Zille9/ESP32-Basic/IMG/amstrad.JPG

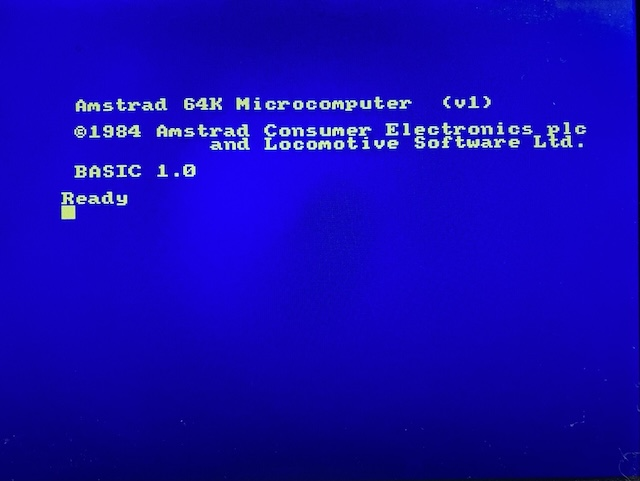
IMG/amstrad.JPG
