Zille9/ESP32-Basic/IMG/App-Starter.JPG

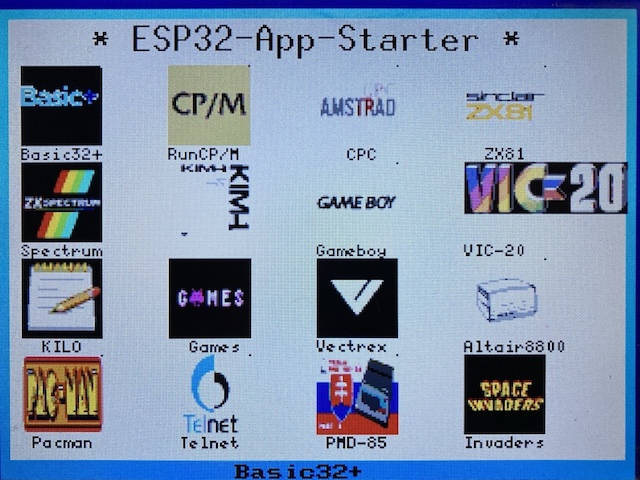
IMG/App-Starter.JPG
