Zille9/ESP32-Basic/IMG/cpc.JPG

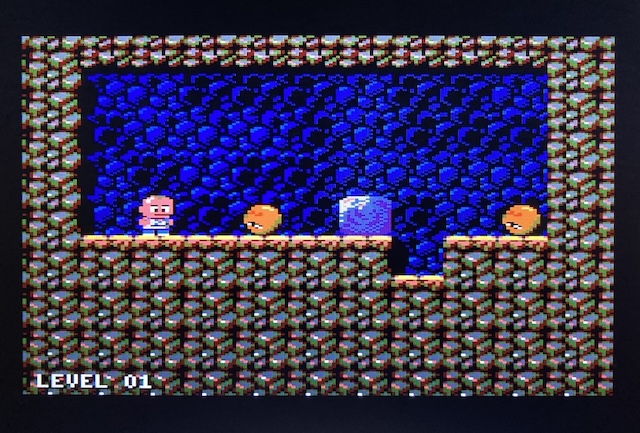
IMG/cpc.JPG
