Zille9/ESP32-Basic/IMG/kilo.JPG

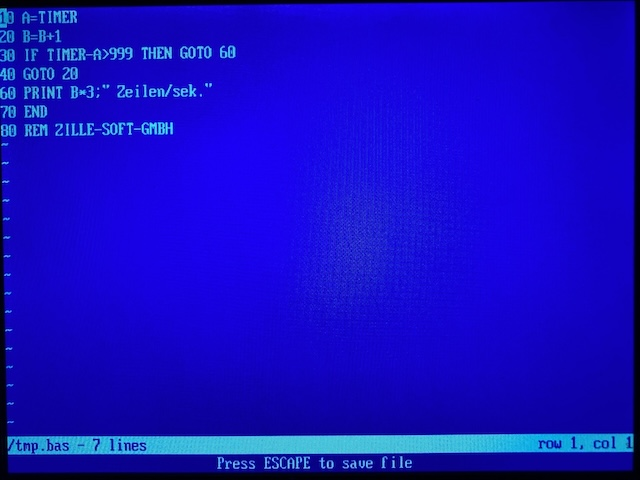
IMG/kilo.JPG
