Zille9/ESP32-Basic/IMG/kim1.JPG

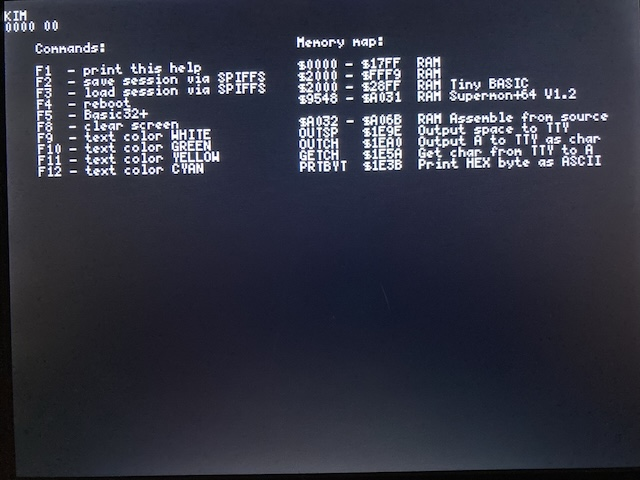
IMG/kim1.JPG
