Zille9/ESP32-Basic/IMG/pacman.JPG

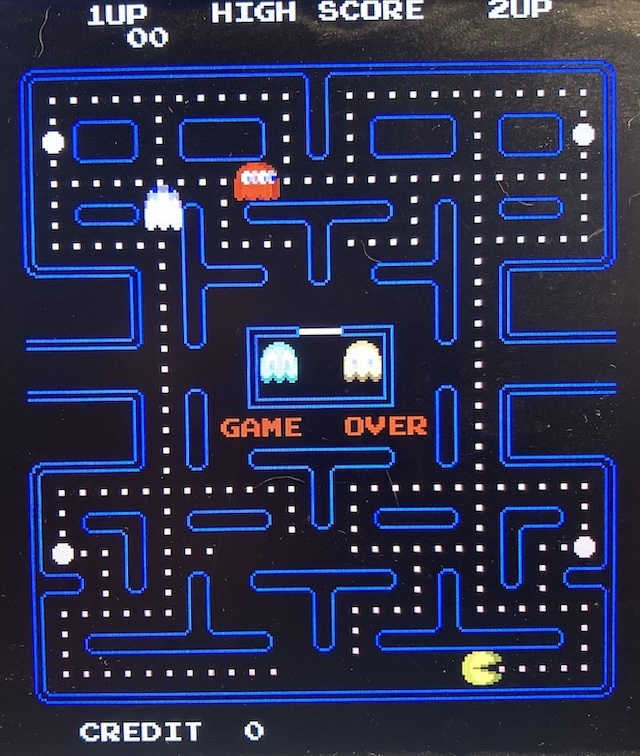
IMG/pacman.JPG
