Zille9/ESP32-Basic/IMG/pmd-85.JPG

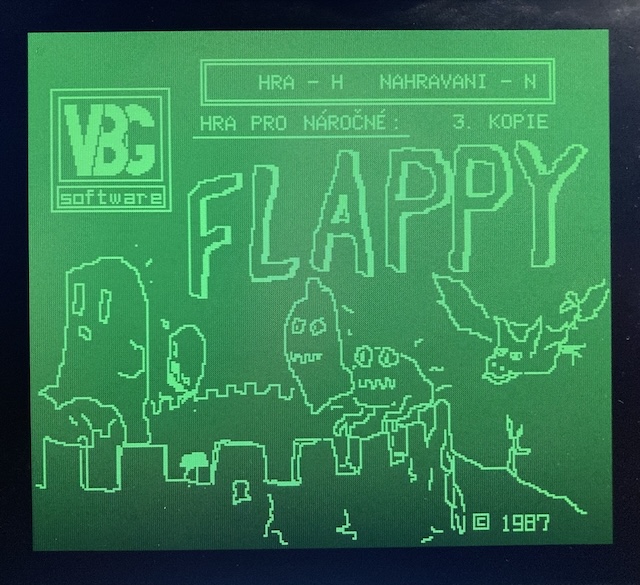
IMG/pmd-85.JPG
