Zille9/ESP32-Basic/IMG/telnet.JPG

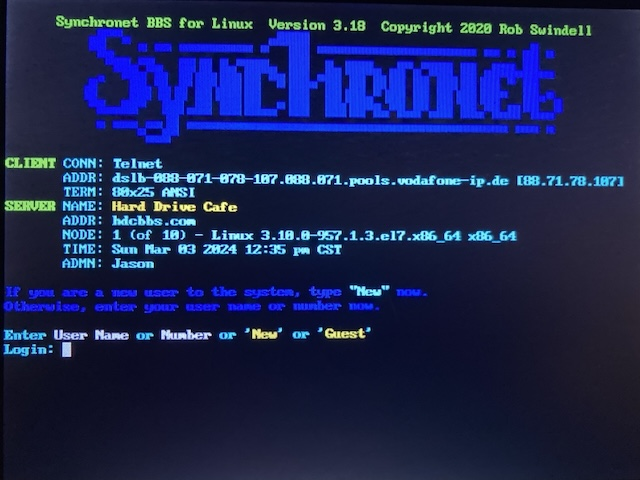
IMG/telnet.JPG
