Zille9/ESP32-Basic/IMG/vectrex.JPG

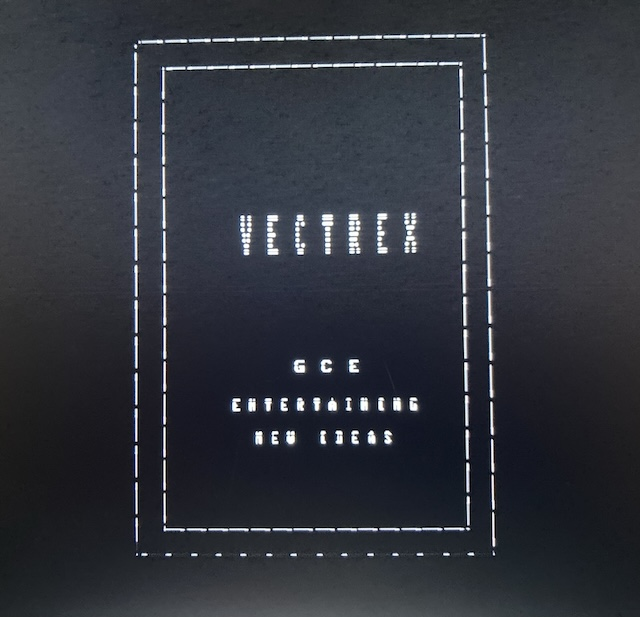
IMG/vectrex.JPG
