Zille9/ESP32-Basic/IMG/vic20.JPG

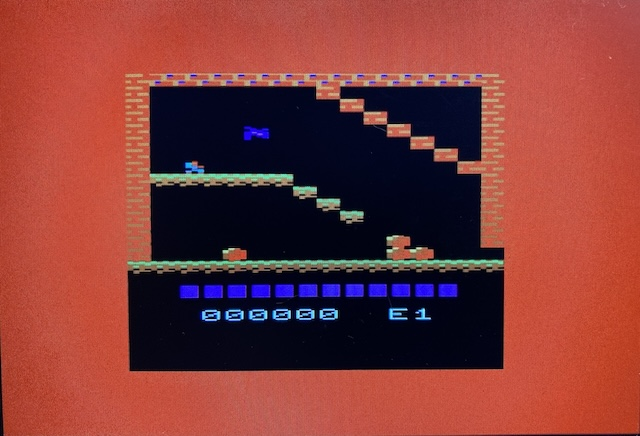
IMG/vic20.JPG
