Zille9/ESP32-Basic/IMG/Webradio.jpg

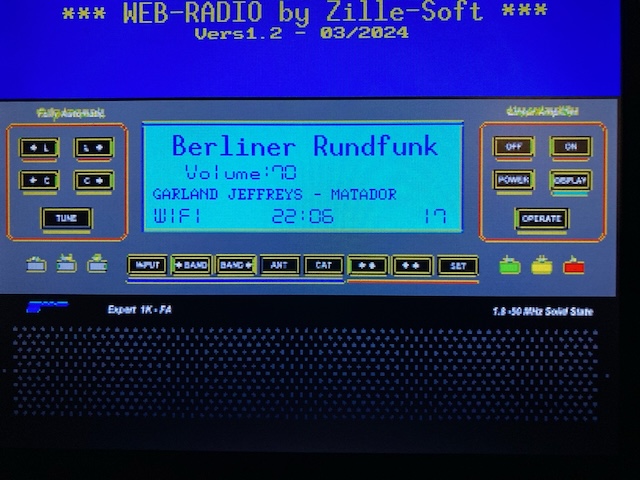
IMG/Webradio.jpg
