Zille9/ESP32-Basic/src/FabGl-Basic/FabGl-Basic.ino

 ///////////////////////////////////////////////////////////////////////////////////////////////////////////////////////////////////////////////////
//             Basic32+ with FabGL VGA library + PS2 PS2Controller                                                                                //
//               for VGA monitor output - May 2019                                                                                                //
//                                                                                                                                                //
//      Ursprungsversion von: Rob Cai <rocaj74@gmail.com>                                                                                         //
//      erweitert/modifiziert von:Reinhard Zielinski <zille09@gmail.com>                                                                          //
//                                                                                                                                                //
//      Connections:                                                                                                                              //
//      PS2Controller Data to ESP32 pin 32;                                                                                                       //
//      PS2Controller IRQ (clock) to ESP32 pin 33;                                                                                                //
//      VGA RGB to ESP32 pin 21,22, 18,19 and 4,5                                                                                                 //
//      VGA Hsync and Vsync to ESP32 pins 23 and 15                                                                                               //
//      SD-Card 14, 16, 17, 13 (SCK, MISO, MOSI, CS)             ESP32-Eigenboard                                                                 //
//      SD-Card 14, 2, 12, 13 (SCK, MISO, MOSI, CS)              TTGO 1.4                                                                         //
//      RAM-Board 14, 16, 17, 0 (SCK, MISO, MOSI, CS)            128,512 o. 8000kB RAM am SD-SPI-BUS                                              //
//      TFT-ILI9341 18, 23, 22, 21, 5 (SCK, MOSI, DC, RESET, CS) TFT-Display ILI9341                                                              //
//                                                                                                                                                //
////////////////////////////////////////////////////////////////////////////////////////////////////////////////////////////////////////////////////
//
// Hinweis: Um die SD-Karte zu verwenden, diese Pinconfiguration verwenden: 14, 16, 17, 13 (SCK, MISO, MOSI, CS)
//          -> Kompatibilität zu fabgl-Programmen (VIC20 Emu, CPM-Emu, ZX-Emu, Tiny-CPC usw.)
//
// Authors: Mike Field <hamster@snap.net.nz>
//	        Scott Lawrence <yorgle@gmail.com>
//          Brian O'Dell <megamemnon@megamemnon.com>
//
// Die Version meiner Vor-Authoren bildet die Grundlage für einen erweiterten Basic-Interpreter
// die Grundversion wurde erweitert durch:  -fliesskomma Arithmetik
//                                          -Grafikfunktionen
//                                          -mathematische Funktionen
//                                          -Stringfunktionen
//                                          -lange Variablennamen
//                                          -viele zusätzliche Befehle (DATA,READ,STRG$,LEFT$,RIGHT$,MID$,POS,TAB,SPC,SIN,COS,TAN,ATN,LOG,SQR,PI usw.)
//                                          -erweiterte logische Operatoren (AND, OR)
//                                          -BIT-Manipulation &,|,%,SL,SR usw.
//                                          -Klammerrechnung
//                                          -IF THEN ELSE Abfragen
//                                          -Speichermonitor
//                                          -Exponential-Ein/Ausgabe
//                                          -Verschiedene Sensoren und Komponenten HC-S04, Dallas DS18S20, DHT, LCD, Neopixel-LED, BMP180
//                                          -Zeileneditor + Texteditor KILO
//                                          -integrierte Kurzhilfe
//
// Author:Reinhard Zielinski <zille09@gmail.com>
// April 2021
//
//
#define BasicVersion "2.06b"
#define BuiltTime "10.05.2024"
// siehe Logbuch.txt zum Entwicklungsverlauf
// v2.06b:10.05.2024          -Fehler in Scroll-Funktion - Anzahl der Parameter war falsch
//                            -16179 Zeilen/sek.
//
// v2.05b:13.04.2024          -Eingabeprompt im Stil des C64 geändert (READY. statt OK>)
//                            -Startbildschirm etwas geschrumpft - Systeminfo's jetzt über F10 abrufbar
//                            -Routine color_out verbessert - keine überstehenden Farbbalken mehr
//                            -16164 Zeilen/sek.
//
// v2.04b:07.04.2024          -Card-KB Treiber etwas angepasst (repeatfunktion) - ZX81 funktioniert (etwas hakelig aber es funktioniert)
//                            -Tastatur wird jetzt auch zuverlässig erkannt
//                            -Ctrl-Tasten-Funktion im Card-KB Treiber eingebunden -> Fn + Buchstabe - Ctrl-C somit wieder funktionstüchtig
//                            -CLEAR löscht jetzt immer die Array-Tabelle (bisher nur, wenn Arrays deklariert waren) - muss vor der ersten Array-Declaration aufgerufen werden (siehe "SOMBRERO.BAS")
//                            -Anzeigeteil der Systemparameter in separate Datei ausgelagert
//                            -Befehl GPX erweitert GPX(x,y,<mode>) mode=0 gibt Pixel gesetzt(1) oder nicht(0) zurück, mode=1 gibt Pixelfarbe zurück
//                            -15972 Zeilen/sek
//
// v2.03b:05.04.2024          -Treiber der Eigenbau-Tastatur ist jetzt zufriedenstellend funktionsfähig, dadurch wurde es nötig die Keyboard-Layout - Umschaltung über den OPT-Befehl
//                            -wieder zugänglich zu machen, das spart die Neucompilierung bei Verwendung unterschiedlicher Tastaturen (Layout steht im EEPROM-Platz 15)
//                            -die Card-KB - Eigenbau - Tastatur erfordert das japanische Layout (Layout 9)
//                            -I2C-Problem mit dem neuen Board, offensichtlich reichen die Pullups des RTC-Moduls für SDA und SCL nicht (bei Netzteilbetrieb), es sind (zumindest für SDA) auf dem Board Pullups notwendig.
//                            -da die Leitungen auf IO1 und IO3 (RX TX) hängen fiel das mit bestehender USB-Verbindung nicht auf (Pegel war hoch genug) - Änderung im Bord-Layout eingepflegt
//                            -und im bestehenden Board zusätzlichen Widerstand eingelötet :-( ärgerlich! -> bei 3,3V muss der Pullup-Widerstand der SDA-Leitung bei ca.2kOhm liegen
//                            -PS2-Treiber der Eigenbau-Tastatur funktioniert nicht bei allen App's - offensichtlich verhält sich eine echte PS2-Tastatur etwas anders als der Eigenbau
//                            -funktionierende Apps: Basic32+, Kilo, VIC20, CPC, ZXESP, Webradio, MP3-Player, Games, ESP-Starter, CPM, Altair, PMD85, Vectrex, Telnet, Invaders - teilweise Tastenanpassungen nötig (Webradio, MP3-Player, Altair, Telnet)
//                            -nicht funktionierende Apps: ESP81, Pacman, Kim1, Gameboy -> keine Reaktion auf Tasteneingaben - Anderer Keyboardtreiber
//                            -SD-Card-Behandlung erweitert - wenn keine oder fehlerhafte Karte detektiert wird
//
// v2.02b:26.03.2024          -neues Board eingetroffen, mit dem es möglich ist SPI-RAM (23LC1024) oder vielleicht sogar PSRAM zu testen, das würde den teuren FRAM ersetzen
//                            -FRAM-Library von Adafruit gekürzt, es wurde die Abfrage der Device-ID deaktiviert. Lt.Datenblatt sollte normaler SPI-RAM und sogar PSRAM ansprechbar sein
//                            -erste Tests bestätigen die Kompatibilität des Treibers für 23LC1024-SPI-Ram Chips - lesen und schreiben funktioniert
//                            -neuer Test mit PSRAM 8MB :-D erfolgreich, somit sind 8MB SPI-Speicher verfügbar allerdings funktioniert alles nur im normalen SPI-Modus
//                            -DSPI oder QSPI sind damit natürlich nicht möglich aber hallo - 8MB, was will man mehr - ist sogar schon etwas zuviel, mal sehen, was mir dazu noch einfällt
//                            -man hat somit 3 unterschiedliche Möglichkeiten der RAM-Unterstützung 128kB-SPI-RAM, 512kB FRAM, 2..4..8MB PSRAM
//                            -FRAM hat den grossen Vorteil, die Daten im ausgeschalteten Zustand nicht zu verlieren und die gleiche Geschwindigkeit und Schreibzyklen (unbegrenzt) wie SPI-Ram zu haben
//                            -ARC-Routine umgebaut, es wird keine cos-Tabelle mehr gebraucht - die Konvertierung Rad in Deg wird berechnet, ausserdem ist die Darstellung genauer
//                            -16500 Zeilen/sek.
//
// v2.01b:19.03.2024          -Grafikbefehl ANGLE erstellt, zeichnet eine Linie von x,y mit dem Winkel w und der länge l -> ANGLE x,y,w,l
//                            -Bildschirmauflösung 320x200 60Hz in fabglconf.h hinzugefügt -> C64 Auflösung, macht die Portierung von Programmen leichter
//                            -Überlegung der Umschaltbarkeit der Auflösungen 320x240 und 320x200 zu integrieren -> funktioniert leider nicht zufriedenstellend
//                            -Umschaltung erfolgt über den OPTION Befehl -> OPT VMODE = mode -> 0 = 320x240, 1 = 320x200(C64 CPC), 2 = 256x192 (ZX Spectrum,TI99), 3=320x256 (KC85), 4=320x192 (Atari 800) und anschliessendem Reboot
//                            -15912 Zeilen/sek - 320x240 , 16500 Zeilen/sek - 320x200, 13539 Zeilen/sek. - 400x300
//
// v2.00b:09.03.2024          -mp3-Player hinzugefügt - ist noch rudimentär aber funktioniert ->RUN"/filename.mp3"
//                            -momentan wird der ID3-Tag als Text ausgeworfen
//                            -ob der Player einen eigenen Befehl (z.Bsp.Play) erhält, ist noch nicht ganz klar (start, stop, pause, nächster- und vorheriger Titel wären nicht schlecht)
//                            -Fehler in der Clear-Routine behoben, es wurden die Variablen im FRam nicht korrekt gelöscht.
//                            -Grafikbefehl ARC erstellt, zeichnet ein Kreis-Teilstück (Tortenstück) ARC x, y, rmin, rmax, grad_start, grad_end, fill
//                            -Grafikbefehl COPY erstellt -> kopiert einen Bildschirmbereich an eine andere Stelle COPY x, y, x_dest, y_dest, width, heigh
//                            -Grafikbefehl SWAP erstellt -> vertauscht die Vorder-und Hintergrundfarbe in einen rechteckigen Bereich SWAP x,y,xx,yy
//                            -16575 Zeilen/sek.
//
//
////////////////////////////////////////////////////////////////////////////////////////////////////////////////////////////////////////////////////
// Konfiguration Grafiktreiber und Akku-Überwachung
#include "cfg.h"   //********************************************* Konfigurations-Datei *************************************************************
#include "fabgl.h" //********************************************* Bibliotheken zur VGA-Signalerzeugung *********************************************
fabgl::Terminal         Terminal;
fabgl::LineEditor       LineEditor(&Terminal);


//---------------------------------------- die verschiedenen Grafiktreiber --------------------------------------------------------------------------
#ifdef AVOUT
fabgl::CVBS16Controller VGAController;    //AV-Variante
#define VIDEOOUT_GPIO GPIO_NUM_26         //Ausgabe auf GPIO25 oder 26 möglich ACHTUNG!:Soundausgabe erfolgt auf GPIO25
static const char * MODES_STD[]   = { "I-PAL-B", "P-PAL-B", "I-NTSC-M", "P-NTSC-M", "I-PAL-B-WIDE", "P-PAL-B-WIDE", "I-NTSC-M-WIDE", "P-NTSC-M-WIDE", "P-NTSC-M-EXT",};

#elif defined VGA64
fabgl::VGAController    VGAController;      //VGA-Variante

#else
fabgl::ILI9341Controller VGAController;     //TFT-Display ILI9341
#endif
//-------------------------------------------------------------------------------------------------------------------------------------------------


//------------------------------------------ Tastatur,GFX-Treiber- und Terminaltreiber -------------------------------------------------------------
fabgl::PS2Controller    PS2Controller;
fabgl::Keyboard Keyboard;
fabgl::Canvas           GFX(&VGAController);
TerminalController      tc(&Terminal);
byte v_mode = 0;                             //Standard-Bildschirmauflösung 320x240
//-------------------------------------------------------------------------------------------------------------------------------------------------

#define erststart_marker 131                //dieser Marker steht im EEprom an Position 100 - wird der ESP32 zum ersten mal mit dem Basic gestartet werden standard-Werte gesetzt
//damit eine benutzbare Version gestartet wird
//---------------------------------------------------- verfügbare Themes ---------------------------------------------------------------------------
const char * Themes[]    PROGMEM = {"C64", "C128", "CPC", "ATARI 800", "ZX-Spectrum", "KC87", "KC85", "VIC-20", "TRS-80", "TI99", "LCD", "User"}; //Theme-Namen
const char * Keylayout[] PROGMEM = {" ", "US", "UK", "GE", "IT", "ES", "FR", "BE", "NO", "JP"};
byte x_char[]      PROGMEM = {8, 5, 6, 8,  10, 8,  8,  8,  8,  8,  8,  8,  8,  6,  8,  4, 6,  7,  7,  8, 8, 8, 6, 9, 8, 8, 6}; //x-werte der Fontsätze zur Berechnung der Terminalbreite
byte y_char[]      PROGMEM = {8, 8, 8, 14, 20, 14, 14, 16, 16, 14, 14, 14, 16, 10, 14, 6, 12, 13, 14, 9, 14, 14, 10, 15, 16, 8, 8}; //y-werte der Fontsätze zur Berechnung der Terminalhöhe

////////////////////////////////////////////////////////////////////////////////////////////////////////////////////////////////////////////////////
//------------------------------------------------------------- Soundgenerator ----------------------------------------------------------------------------
unsigned int noteTable []  PROGMEM = {16350, 17320, 18350, 19450, 20600, 21830, 23120, 24500, 25960, 27500, 29140, 30870}; //Notentabelle für Soundausgabe
//------------------------------------------------------------- Soundgenerator ----------------------------------------------------------------------------

//----------------------------------- Editor -Marker ----------------------------------------------------------------------------------------------
byte Editor_marker = 101;            // EEPROM-Platz 101 beinhaltet den Editor-marker (123) lädt die Datei tmp.bas nach Rückkehr vom Kilo-Editor
//-------------------------------------------------------------------------------------------------------------------------------------------------

// ---------------------------------- SD-Karten-Zugriff--------------------------------------------------------------------------------------------
#include <SD.h>
#include <SPI.h>
//SPI CLASS FOR REDEFINED SPI PINS !
SPIClass spiSD(HSPI);
File fp;
//-------------------------------------------------------------------------------------------------------------------------------------------------

//------------------------------------- OTA-Update-Lib --------------------------------------------------------------------------------------------
#include <Update.h>
//-------------------------------------------------------------------------------------------------------------------------------------------------
/*
//------------------------------------- SPRITES --------------------------------------------------------------------------------------------
#include <collisiondetector.h>
//-------------------------------------------------------------------------------------------------------------------------------------------------
*/

//------------------------------------- ESP32-Time-Lib fuer Datei-zeitstempel ---------------------------------------------------------------------
#include <ESP32Time.h>
ESP32Time e_rtc(0);  // offset in seconds GMT+1
//-------------------------------------------------------------------------------------------------------------------------------------------------

//------------------------------------- Mathematische Funktionen fuer printnum --------------------------------------------------------------------
#include "MathHelpers.h"
//-------------------------------------------------------------------------------------------------------------------------------------------------


// ------------------------------ Dallas Temp-Sensor ----------------------------------------------------------------------------------------------
#include <OneWire.h>
#include <DallasTemperature.h>
bool twire = false;
//-------------------------------------------------------------------------------------------------------------------------------------------------

//--------------------------------- DHT-Sensor ----------------------------------------------------------------------------------------------------
#include <Adafruit_Sensor.h>
#include <DHT.h>
#include <DHT_U.h>
uint32_t delayMS;
//-------------------------------------------------------------------------------------------------------------------------------------------------

//-------------------------------- BMP180-Sensor --------------------------------------------------------------------------------------------------
#include <Adafruit_Sensor.h>
#include <Adafruit_BMP085.h>
// Store an instance of the BMP180 sensor.
Adafruit_BMP085 bmp;
// Store the current sea level pressure at your location in Pascals.
float seaLevelPressure = SENSORS_PRESSURE_SEALEVELHPA;
//-------------------------------------------------------------------------------------------------------------------------------------------------

// -------------------------- EEPROM Routinen für Parameter-Speicherung ---------------------------------------------------------------------------
#include <EEPROM.h>
#define EEPROM_SIZE 512  //512 byte lesen/speichern
//-------------------------------------------------------------------------------------------------------------------------------------------------

//---------------------------- EEPROM o.FRAM-Chip I2C-Adressen ------------------------------------------------------------------------------------

short int EEprom_ADDR = 0x50; //-> Adresse 0x50 ist der EEPROM auf dem Board
//short int EEprom_ADDR = 0x57; //-> Adresse 0x57 ist der EEPROM auf dem RTC3231 Board
//-------------------------------------------------------------------------------------------------------------------------------------------------


// ---------------------------- W2812-seriell LED-Treiber -----------------------------------------------------------------------------------------
#include <Adafruit_NeoPixel.h>
unsigned int LED_COUNT      = 255;
unsigned int LED_PIN        = 2;
unsigned int LED_BRIGHTNESS = 50;
unsigned int LED_TYP        = 2;
Adafruit_NeoPixel strip(LED_COUNT, LED_PIN, NEO_GRB + NEO_KHZ800);                //WS2812
//-------------------------------------------------------------------------------------------------------------------------------------------------

//------------------------------ MCP23017 IO-Expander ---------------------------------------------------------------------------------------------
#include <Adafruit_MCP23X17.h>   //Adafruit MCP23xx Treiber
Adafruit_MCP23X17 mcp;
short int MCP23017_ADDR = 0x20 ; //Adresse 32 (0x20) für eingebauten MCP23017
bool mcp_start_marker = false;
//-------------------------------------------------------------------------------------------------------------------------------------------------

//------------------------------ I2C Library ------------------------------------------------------------------------------------------------------
#include <Wire.h>           // for I2C 
#include "RTClib.h"         //to show time
TwoWire myI2C = TwoWire(0); //eigenen I2C-Bus erstellen
RTC_DS3231 rtc;
//diese Konstellation funktioniert mit ESP-Eigenboard und RTC-Modul oder 27 und 26 für die Freigabe des Seriellports
byte IIC_SET = 55;      // -steht 55 im EEprom-Platz 13, dann sind die Werte im EEprom gültig
// dies ist die Standard-Konfiguration
byte SDA_RTC = 3;
byte SCL_RTC = 1;
//-------------------------------------------------------------------------------------------------------------------------------------------------

//-------------------------------------- LCD-Treiber ----------------------------------------------------------------------------------------------
#include "HD44780_LCD_PCF8574.h"
#define DISPLAY_DELAY_INIT 50 // mS
int LCD_SPALTEN, LCD_ZEILEN, LCD_ADRESSE, LCD_NACHKOMMA;
bool LCD_start_marker = false;
bool LCD_Backlight = true;
//-------------------------------------------------------------------------------------------------------------------------------------------------

//######################################### Anfang Konfiguration SPI-RAM ##########################################################################
//------------------------------------------- SPI-RAM-Lib -----------------------------------------------------------------------------------------
#include "Adafruit_FRAM_SPI.h"        // Library unterstützt 23LC1024, Adafruit SPI-FRAM und PSRAM

byte FRAM_CS  = 0;                    //SPI-RAM CS-Pin
Adafruit_FRAM_SPI spi_fram = Adafruit_FRAM_SPI(kSD_CLK, kSD_MISO, kSD_MOSI, FRAM_CS);

//---------------------------------------- spezielle SPI-Ram-Adressen -----------------------------------------------------------------------------
word FRAM_OFFSET      = 0x8000;     //Offset für Poke-Anweisungen, um zu verhindern, das in den Array-Bereich gepoked wird
word FRAM_PIC_OFFSET  = 0x12C04;    //Platz pro Bildschirm im Speicher 320x240=76800 + 4Byte für die Dimension = 76804
long load_adress      = 0x8000;     //ab hier kann ein Basicprogramm abgelegt werden (Eingabe: LOAD oder SAVE ohne Parameter)

//---------------------------------------- Array-Parameter ----------------------------------------------------------------------------------------
//Der Arraybereich befindet sich 0x0..0x7fff
word Var_Neu_Platz =  0;            //Adresse nächstes Array-Feld Start bei 0x77e00
static word VAR_TBL = 0x7e00;       //Variablen-Array-Tabelle im SPI-RAM
static word STR_TBL = 0x7f00;       //String-Array-Tabelle im SPI-RAM
//-------------------------------------------------------------------------------------------------------------------------------------------------
//######################################### Ende Konfiguration SPI-RAM ############################################################################



//------------------------------- Konfiguration serielle Schnittstelle ----------------------------------------------------------------------------
uint8_t prx, ptx;             //RX- und TX-Pin
uint32_t pbd;                 //Baudrate
bool ser_marker = false;      //seriell-Marker, wenn gesetzt erfolgt jede Printausgabe auch auf die serielle Schnittstelle
bool list_send = false;
bool serout_marker = false;
#define SERIAL_SIZE_RX 1024
//-------------------------------------------------------------------------------------------------------------------------------------------------

//------------------------------------------------ Startparameterauswahl --------------------------------------------------------------------------
byte Keyboard_lang = KLayout; //Tastatur-Layout (cfg.h) - Standardeinstellung=German
byte THEME_SET = 77;    //-steht 77 im EEPROM Platz 17, dann setze das gespeicherte Theme
byte PATH_SET = 88;     //-steht 88 im EEPROM Platz 19, dann setze Arbeits-Pfad
//-------------------------------------------------------------------------------------------------------------------------------------------------

//------------------------------------- Akku-Überwachung ------------------------------------------------------------------------------------------
#ifdef Akkualarm_enabled            // Akku-Überwachung für batteriebetriebene Geräte
hw_timer_t *Akku_timer = NULL;      //Interrupt-Routine Akku-Überwachung
#endif
#define Batt_Pin 39                 //Pin wird in jedem Fall definiert
//-------------------------------------------------------------------------------------------------------------------------------------------------

//------------------------------- BMP-Info-Parameter für PIC-Befehl -------------------------------------------------------------------------------
uint32_t bmp_width, bmp_height;
//-------------------------------------------------------------------------------------------------------------------------------------------------

#define bool int
#define true 1
#define false 0

//für Texte/Zeichenketten im Flash
#ifndef PROGMEM
#define PROGMEM
#endif
#ifndef pgm_read_byte
#define pgm_read_byte( A ) *(A)
#endif

#define STR_LEN 40
#define STR_SIZE 26*STR_LEN             //Stringspeicher = Stringlänge 26*40 Zeichen (A..Z * 40 Zeichen)

//------------------------------ hier wird der Funktionsstring gespeichert ------------------------------------------------------------------------
#define FN_SIZE STR_LEN                 //Funktionsspeicher für benutzerdefinierte Funktionen mit bis zu vier Operatoren-> FN A(A,B,C,D)

bool inhibitOutput = false;
static bool autorun = false;            //Programm nach dem Laden automatisch starten
static bool triggerRun = false;

short int Vordergrund = 43;             //Standard-Vordergrundfarbe (wenn noch nichts im EEprom steht)
short int Hintergrund = 18;             //Standard-Hintergrundfarbe (wenn noch nichts im EEprom steht)
short int fontsatz = 0;                 //Nummer des ausgewählten Fontsatzes
short int user_vcolor = Vordergrund;    //User-Vordergrundfarbe
short int user_bcolor = Hintergrund;    //User-Hintergrundfarbe
short int user_font = fontsatz;         //User-Fontsatz

short int Prezision = 6;                //Standardfestlegung der Nachkommastellen
static bool chr = false;                //marker für CHR$ für Print
static bool string_marker = false;      //marker für Strings (Print)
static bool func_string_marker = false; //marker für String$-Funktion (Print)
static bool tab_marker = false;         //marker für TAB (Print)
static bool semicolon = false;          //marker für semikolon (Print)
static byte fstring = 0;                //Übergabewert für STRING$(n,"string")
short int Theme_state = 0;              //aktuelle Theme Nummer (im EEPROM gespeichert)
static bool Theme_marker = false;       //Theme-Marker, falls Farben geändert
short int Mode_state = 0;               //aktuelle Auflösung (im EEProm gespeichert)

static bool break_marker = false;      //********** Test für CardKB *****************

uint8_t curGain = 100;                 //current loudness Audiolautstärke
int Key_l = 0;                         //Tasten für MP3-Player
int Key_r = 0;
int Key_u = 0;
int Key_d = 0;

//------------------------------ Grid-Parameter ---------------------------------------------------------------------------------------------------
int Grid[15];  //0=x, 1=y, 2=xx, 3=yy, 4=zell_x, 5=zell_y, 6=pix_x, 7=pix_y, 8=frame-col, 9=grid_col
int Grid_point_x, Grid_point_y;

//------------------------------ Window-Parameter -------------------------------------------------------------------------------------------------

int Frame_nr;                 //5 Fenster können erstellt werden
int Frame_x[6];
int Frame_y[6];
int Frame_xx[6];
int Frame_yy[6];
int Frame_curx[6];            //X-Cursor Initialwert
int Frame_curtmpx[6];         //X-Cursor temporärer Wert
int Frame_curtmpy[6];         //Y-Cursor temporärer Wert
int Frame_cury[6];            //Y-Cursor Initialwert
int Frame_col[6];             //Rahmenfarbe
int Cursor_x, Cursor_y;       //temporäre Cursorpositionen
int Frame_vcol[6];            //Vordergrundfarbe
int Frame_hcol[6];            //Hintergrundfarbe
bool Frame_title[6];          //Titeltext
char Frame_ttext[6][STR_LEN]; //Fenster-Titel-String

//-------------------------------------------------------------------------------------------------------------------------------------------------

short int onoff = 1;          //Cursor status

//-------------------------------------------------------------------------------------------------------------------------------------------------

// these will select, at runtime, where IO happens through for load/save
enum {
  kStreamTerminal = 0,
  kStreamFile,
  kStreamSerial,
  kStreamFram
};
static char inStream = kStreamTerminal;
static char outStream = kStreamTerminal;

static char program[kRamSize];            //Basic-Programmspeicher
static char Stringtable[STR_SIZE];        //Stringvariablen mit 1 Buchstaben -> 26*40 = 1040 Bytes
//-------------------------------------------------------------------------------------------------------------------------------------------------

//------------------------------------- DEFN - FN -------------------------------------------------------------------------------------------------
static char Fntable[26][FN_SIZE];         // bytes 40 String = 40*26 ->1040 bytes ->Funktionsstring-Array
int Fnvar = 0;                            //Operatorenzähler
int Fnoperator[27 * 5];                   //DEFN A(a,b,c,d,e,f,g,h)-> Name 0-26,0-26=Operator1,0-26=operator2,0-26=Operator3,0-26=Operator4 + 1 Anzahl
bool fn_marker = false;

//------------------------------------ Editor -----------------------------------------------------------------------------------------------------
char const * Edit_line = nullptr;        //Editor-Zeile
long editpos;                            //Position innerhalb des Programs
//------------------------------------ Interpreter ------------------------------------------------------------------------------------------------
char tempstring[STR_LEN];                //String Zwischenspeicher

//------------------------------------ Dateifunktionen FREAD,FWRITE -------------------------------------------------------------------------------
char filestring[STR_LEN];                //Namensstring für Dateioperationen Fread,Fwrite
static bool Datei_open = false;          //FREAD, FWRITE Open-marker
long File_pos = 0;                       //Dateipositions-merker der geöffneten Datei
long File_size = 0;                      //Dateigrösse der geöffneten Datei

static char *txtpos, *list_line, *tmptxtpos, *dataline;
static char expression_error;
static char *tempsp;
static char sd_pfad[STR_LEN];            //SD-Card Datei-Pfad

char path1[STR_LEN], path2[STR_LEN];     //Variablen für Dateioperationen
unsigned int Datum[4];                   //Datums-Array
unsigned int Zeit[4];                    //Zeit-Array

//----------------------------------------- DATA Variablen ----------------------------------------------------------------------------------------
unsigned int datapointer = 0;       //data-Zeiger innerhalb des Datanfeldes
unsigned int restorepointer = 0;    //begin des Datanfeldes
unsigned int num_of_datalines = 0;  //Anzahl DATA-Zeilen
unsigned int current_dataline = 0;  //aktuelle DATA-Zeile
unsigned int data_numbers[300];     //Array zur speicherung von 300 DATA Zeilennummern

//////////////////////////////////////////////////////////////////////////////////////////////////////////////////////////////////////////////////
// ASCII Characters
#define CR	'\r'
#define NL	'\n'
#define LF  0x0a
#define TAB	'\t'
#define BELL	'\b'
#define SPACE   ' '
#define SQUOTE  '\''
#define DQUOTE  '\"'
#define CTRLC	0x03
#define CTRLH	0x08
#define CTRLS	0x13

bool Graph_char = false;                               //Grafiksymbole "AUS"
bool tron_marker = false;                              //TRON "AUS"

typedef short unsigned LINENUM;

/***************************Basic-Befehle ********************************/
// Keyword table and constants - the last character has 0x80 added to it
const static char keywords[] PROGMEM = {
  'L', 'I', 'S', 'T' + 0x80,
  'L', 'O', 'A', 'D' + 0x80,
  'N', 'E', 'W' + 0x80,
  'R', 'U', 'N' + 0x80,
  'S', 'A', 'V', 'E' + 0x80,
  'N', 'E', 'X', 'T' + 0x80,
  'R', 'E', 'N' + 0x80,
  'I', 'F' + 0x80,
  'G', 'O', 'T', 'O' + 0x80,
  'G', 'O', 'S', 'U', 'B' + 0x80,
  'R', 'E', 'T', 'U', 'R', 'N' + 0x80,
  'R', 'E', 'M' + 0x80,
  'F', 'O', 'R' + 0x80,
  'I', 'N', 'P', 'U', 'T' + 0x80,
  'P', 'R', 'I', 'N', 'T' + 0x80,
  'P', 'O', 'K', 'E' + 0x80,
  'D', 'I', 'R' + 0x80,
  'C', 'L', 'S' + 0x80,
  'P', 'O', 'S' + 0x80,
  'C', 'O', 'L' + 0x80,
  'P', 'S', 'E', 'T' + 0x80,
  'C', 'I', 'R', 'C' + 0x80,
  'L', 'I', 'N', 'E' + 0x80,
  'R', 'E', 'C', 'T' + 0x80,
  'F', 'O', 'N', 'T' + 0x80,
  'P', 'A', 'U', 'S', 'E' + 0x80,
  'E', 'N', 'D' + 0x80,
  'C', 'L', 'E', 'A', 'R' + 0x80,
  'T', 'H', 'E', 'N' + 0x80,
  'E', 'L', 'S', 'E' + 0x80,
  'C', 'U', 'R' + 0x80,
  'P', 'R', 'Z' + 0x80,
  'D', 'M', 'P' + 0x80,
  'S', 'T', 'Y', 'L', 'E' + 0x80,
  'S', 'C', 'R', 'O', 'L', 'L' + 0x80,
  'T', 'H', 'E', 'M', 'E' + 0x80,
  'D', 'A', 'T', 'A' + 0x80,
  'R', 'E', 'A', 'D' + 0x80,
  'R', 'E', 'S', 'T', 'O', 'R', 'E' + 0x80,
  'D', 'E', 'L' + 0x80,
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
};

// by moving the command list to an enum, we can easily remove sections
// above and below simultaneously to selectively obliterate functionality.
enum {
  KW_LIST = 0,
  KW_LOAD,
  KW_NEW,
  KW_RUN,
  KW_SAVE,
  KW_NEXT,
  KW_REN,
  KW_IF,
  KW_GOTO,
  KW_GOSUB,
  KW_RETURN,    //10
  KW_REM,
  KW_FOR,
  KW_INPUT,
  KW_PRINT,
  KW_POKE,
  KW_DIR,
  KW_CLS,
  KW_POS,
  KW_COLOR,
  KW_PSET,      //20
  KW_CIRCLE,
  KW_LINE,
  KW_RECT,
  KW_FONT,
  KW_DELAY,
  KW_END,
  KW_CLEAR,
  KW_THEN,
  KW_ELSE,
  KW_CURSOR,    //30
  KW_PREZISION,
  KW_DUMP,
  KW_STYLE,
  KW_SCROLL,
  KW_THEME,
  KW_DATA,
  KW_READ,
  KW_RESTORE,
  KW_DEL,
  KW_AND,       //40
  KW_OR,
  KW_SRTC,
  KW_IIC,
  KW_DWRITE,
  KW_PWM,
  KW_DAC,
  KW_DRAW,
  KW_SPRITE,
  KW_PULSE,
  KW_SOUND,    //50
  KW_PEN,
  KW_ON,
  KW_LCD,
  KW_MCPPORT,
  KW_MCPPIN,
  KW_CHDIR,
  KW_MKDIR,
  KW_RMDIR,
  KW_DEFFUNC,
  KW_LED,     //60
  KW_EDIT,
  KW_DOKE,
  KW_BEEP,
  KW_DIM,
  KW_OPTION,
  KW_FPOKE,
  KW_MOUNT,
  KW_COM,
  KW_PIC,
  KW_OPEN,    //70
  KW_CLOSE,
  KW_FILE,
  KW_TYPE,
  KW_GRID,
  KW_TEXT,
  KW_PRINTING,
  KW_WINDOW,
  KW_HELP,
  KW_FRAME,
  KW_ARC,     //80
  KW_SWAP,
  KW_COPY,
  KW_ANGLE,
  //KW_BAR,
  KW_DEFAULT  //85/* hier ist das Ende */
};

int KW_WORDS = KW_DEFAULT;

// Variablen zur Zwischenspeicherung von logischen Operationen (AND OR)

int logic_counter;
int logic_ergebnis[10];

//-> bis zu 5 AND oder OR Vergleiche können in einer Zeile vorkommen

struct stack_for_frame {
  char frame_type;    //1byte
  int for_var;        //2byte
  float to_var;       //4byte
  float step;         //4byte
  char *current_line; //1byte
  char *txtpos;       //1byte
};

struct stack_gosub_frame {
  char frame_type;
  char *current_line;
  char *txtpos;
};

#define User_Ram (kRamSize-STACK_SIZE-(26 * 27 * VAR_SIZE))

//**************************** Basic-Funktionen *********************************
const static char func_tab[] PROGMEM = {
  'P', 'E', 'E', 'K' + 0x80,
  'A', 'B', 'S' + 0x80,
  'R', 'N', 'D' + 0x80,
  'S', 'I', 'N' + 0x80,
  'C', 'O', 'S' + 0x80,
  'T', 'A', 'N' + 0x80,
  'L', 'O', 'G' + 0x80,
  'S', 'G', 'N' + 0x80,
  'S', 'Q', 'R' + 0x80,
  'I', 'N', 'T' + 0x80,
  'M', 'I', 'N' + 0x80,
  'M', 'A', 'X' + 0x80,
  'E', 'X', 'P' + 0x80,
  'G', 'E', 'T' + 0x80,
  'C', 'H', 'R', '$' + 0x80,
  'I', 'N', 'K', 'E', 'Y' + 0x80,
  'F', 'O', 'N', 'T' + 0x80,
  'A', 'S', 'C' + 0x80,
  'T', 'I', 'M', 'E', 'R' + 0x80,
  'A', 'T', 'N' + 0x80,
  'L', 'E', 'N' + 0x80,
  'I', 'N', 'S', 'T', 'R' + 0x80,
  'C', 'O', 'M', 'P', '$' + 0x80,
  'B', 'I', 'N' + 0x80,
  'H', 'E', 'X' + 0x80,
  'L', 'E', 'F', 'T', '$' + 0x80,
  'R', 'I', 'G', 'H', 'T', '$' + 0x80,
  'M', 'I', 'D', '$' + 0x80,
  'T', 'A', 'B' + 0x80,
  'S', 'P', 'C' + 0x80,
  'S', 'T', 'R', '$' + 0x80,
  'D', 'A', 'T', 'E' + 0x80,
  'T', 'I', 'M', 'E' + 0x80,
  'I', 'I', 'C' + 0x80,
  'A', 'K', 'K', 'U' + 0x80,
  'A', 'I', 'N' + 0x80,
  'D', 'I', 'N' + 0x80,
  'U', 'C', '$' + 0x80,
  'L', 'C', '$' + 0x80,
  'V', 'A', 'L' + 0x80,
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
};

enum {
  FUNC_PEEK = 0,
  FUNC_ABS,
  FUNC_RND,
  FUNC_SIN,
  FUNC_COS,
  FUNC_TAN,
  FUNC_LOG,
  FUNC_SGN,
  FUNC_SQR,
  FUNC_INT,
  FUNC_MIN,     //10
  FUNC_MAX,
  FUNC_EXP,
  FUNC_GET,
  FUNC_CHR,
  FUNC_INKEY,
  FUNC_FONT,
  FUNC_ASC,
  FUNC_TIMER,
  FUNC_ATAN,
  FUNC_LEN,       //20
  FUNC_INSTR,
  FUNC_COMPARE,
  FUNC_BIN,
  FUNC_HEX,
  FUNC_LEFT,
  FUNC_RIGHT,
  FUNC_MID,
  FUNC_TAB,
  FUNC_SPC,
  FUNC_STR,       //30
  FUNC_GDATE,
  FUNC_GTIME,
  FUNC_IIC,
  FUNC_BATT,
  FUNC_AREAD,
  FUNC_DREAD,
  FUNC_UCASE,
  FUNC_LCASE,
  FUNC_VAL,
  FUNC_MEM,      //40
  FUNC_NOT,
  FUNC_TEMP,
  FUNC_DHT,
  FUNC_GETCOL,
  FUNC_BMPREAD,  //ungetestet BMP180 Drucksensor
  FUNC_FN,
  FUNC_PORT,
  FUNC_PIN,
  FUNC_PI,
  FUNC_LN,       //50
  FUNC_DEEK,
  FUNC_FPEEK,
  FUNC_GPIX,
  FUNC_PIC,
  FUNC_MAP,
  FUNC_CONSTRAIN,
  FUNC_STRING,
  FUNC_FILE,
  FUNC_GRID,
  FUNC_UNKNOWN   //60
};

int FUNC_WORDS = FUNC_UNKNOWN;

//------------------------------- OPTION-Tabelle - alle Optionen, die dauerhaft gespeichert werden sollen -----------------------------------------
const static char options[] PROGMEM = {
  'V', 'M', 'O', 'D', 'E' + 0x80,           //VGA-Modus 0=320x240, 1=320x200
  'F', 'R', 'A', 'M' + 0x80,                //CS-Pin FRAM
  'E', 'E', 'P', 'R', 'O', 'M' + 0x80,      //Adresse des I2C-EEproms
  'F', 'O', 'N', 'T' + 0x80,                //Font dauerhaft speichern
  'C', 'O', 'L' , 'O', 'R' + 0x80,          //Vordergrund- und Hintergrundfarbe dauerhaft speichern
  'K', 'E', 'Y' + 0x80,                     //Keyboardlayout 1=US,2=UK,3=GE,4=IT,5=ES,6=FR,7=BE,8=NO,9=JP
  'T', 'H', 'E', 'M', 'E' + 0x80,           //THEME
  'P', 'A', 'T', 'H' + 0x80,                //Arbeitsverzeichnis

  0
};

enum {
  OPT_VMODE = 0,
  OPT_FRAM,
  OPT_EEP,
  OPT_FONT,
  OPT_COLOR,
  OPT_KEYBOARD,
  OPT_THEME,
  OPT_PATH,
  OPT_UNKNOWN  //8
};
//-------------------------------------------------------------------------------------------------------------------------------------------------


const static char to_tab[] PROGMEM = {
  'T', 'O' + 0x80,
  0
};

const static char step_tab[] PROGMEM = {
  'S', 'T', 'E', 'P' + 0x80,
  0
};

const static char relop_tab[] PROGMEM = {
  '>', '=' + 0x80,  //größer gleich
  '<', '>' + 0x80,  //ungleich
  '>', '>' + 0x80,  //SHIFT RIGHT
  '>' + 0x80,       //größer
  '=' + 0x80,       //gleich
  '<', '=' + 0x80,  //kleiner gleich
  '<', '<' + 0x80,  //SHIFT LEFT
  '|', '|' + 0x80,  //XOR
  '<' + 0x80,       //kleiner
  '%' + 0x80,       //MODULO
  '&' + 0x80,       //AND
  '|' + 0x80,       //OR
  '^' + 0x80,       //POW
  0
};

#define RELOP_GE		0
#define RELOP_NE		1
#define RELOP_SHR   2
#define RELOP_GT		3
#define RELOP_EQ		4
#define RELOP_LE		5
#define RELOP_SHL   6
#define RELOP_XOR   7
#define RELOP_LT		8
#define RELOP_MOD   9
#define RELOP_AND   10
#define RELOP_OR    11
#define RELOP_POW   12
#define RELOP_UNKNOWN	13

#define STACK_SIZE (sizeof(struct stack_for_frame)*26)   // 26 verschachtelte For-Next-Schleifen erlaubt (32bytes pro frame) 
#define VAR_SIZE sizeof(float)                           // Variablengrösse für float 4Bytes
static char *stack_limit;
static char *program_start;
static char *program_end;
static char *stack; // Software stack for things that should go on the CPU stack
static char *variables_begin;
static char *current_line;
static char *data_line;
static char *sp;
#define STACK_GOSUB_FLAG 'G'
#define STACK_FOR_FLAG 'F'
static char table_index;
static char keyword_index;
static LINENUM linenum;

//---------------------------------- Fehlermeldungen des Interpreters -----------------------------------------------------------------------------

static const char syntaxmsg[]        PROGMEM = "Syntax Error! ";                //1
static const char mathmsg[]          PROGMEM = "Math Error!";                   //2
static const char gosubmsg[]         PROGMEM = "Gosub Error!";                  //3
static const char fornextmsg[]       PROGMEM = "For-Next Error!";               //4
static const char memorymsg[]        PROGMEM = " bytes free";
static const char missing_then[]     PROGMEM = "Missing THEN Error!";           //5
static const char breakmsg[]         PROGMEM = "Break! in Line:";
static const char breaks[]           PROGMEM = "Break!";
static const char datamsg[]          PROGMEM = "Out of DATA Error!";            //6
static const char invalidmsg[]       PROGMEM = "Invalid comparison!";           //7
static const char sderrormsg[]       PROGMEM = "SD card error.";                //8
static const char sdfilemsg[]        PROGMEM = "SD file error.";                //9
static const char dirextmsg[]        PROGMEM = "(dir)";
static const char slashmsg[]         PROGMEM = "/";
static const char spacemsg[]         PROGMEM = " ";
static const char notexistmsg[]      PROGMEM = "File not exist!";               //10
static const char portmsg[]          PROGMEM = "Wrong Port-Number!";            //11
static const char valmsg[]           PROGMEM = "Invalid Value!";                //12
static const char dirmsg[]           PROGMEM = "Dir not empty!";                //13
static const char illegalmsg[]       PROGMEM = "Illegal quantity Error!";       //14
static const char zeroerror[]        PROGMEM = "Div/0-Error!";                  //15
static const char outofmemory[]      PROGMEM = "Out of Memory Error!";          //16
static const char mountmsg[]         PROGMEM = "SD-Card mounted";               //17
static const char notmount[]         PROGMEM = "SD-Card can't mount";           //18
static const char dimmsg[]           PROGMEM = "Array-Dimension Error!";        //19
static const char commsg[]           PROGMEM = "No COM-Port defined!";          //20
static const char comsetmsg[]        PROGMEM = "Wrong COM-Port Definition!";    //21
static const char bmpfilemsg[]       PROGMEM = "No BMP-File!";                  //22
static const char no_prg_msg[]       PROGMEM = "No Program in Memory !";        //23
static const char no_command_msg[]   PROGMEM = "Keyword not found !";           //24
static const char not_openmsg[]      PROGMEM = "File not open Error !";         //25
static const char dirnotfound[]      PROGMEM = "DIR not found !";               //26
static const char extension_error[]  PROGMEM = "invalid File-Extension !";      //27
//----------------------------------- Interpreter-Variablen ---------------------------------------------------------------------------------------
char *pstart;
char *newEnd;
char linelen;
bool then_marker = false;
bool else_marker = false;
float val;
int Zahlenformat = 0;
int logica = 0;                          //logikzähler für IF abfragen
unsigned int ongosub = 0;                //ON-Gosub Goto marker
//----------------------------------- Interpreter-Variablen ---------------------------------------------------------------------------------------
//#################################################################################################################################################
//############################################# Ende Deklarationsungsbereich ######################################################################
//#################################################################################################################################################

//--------------------------------------------- Ausgabe Fehlermeldungen ---------------------------------------------------------------------------
static char syntaxerror(const char *msg)
{
  printmsg(msg, 1);
  if (current_line != NULL)
  {
    char tmp = *txtpos;           //Position merken
    if (*txtpos != NL) *txtpos = '^';
    list_line = current_line;
    printline();
    *txtpos = tmp;                //gemerkte Position zurückschreiben
  }
  Beep(0, 0);                     //Error-BEEP
  current_line = 0;
  line_terminator();
}

float NoteToFreq(int mnote)
{
  int octave;
  octave = mnote / 12;
  mnote -= octave * 12;
  return noteTable[mnote] >> (8 - octave);
}

void Beep(int n, int len)
{
  if (n == 0) n = 60;
  if (len == 0) len = 100;
  if (n > 80) n = 80;
  if (n < 20) n = 20;
  n = NoteToFreq(n);
  //SND(waveform,frequency,duration,volume)

  Terminal.print("\e_S0;" + String(n, DEC) + ";" + String(len, DEC) + ";126$");
  delay(len);
}

//--------------------------------------------- Unterprogramm - Zeichen überspringen --------------------------------------------------------------
//--------------------------------------------- nächstes Zeichen zurückgeben ----------------------------------------------------------------------

static char skip_spaces(void) {
  if (*txtpos)
  {
    txtpos++;
    return spaces();
  }
}


//--------------------------------------------- Unterprogramm - Leerzeichen überspringen ----------------------------------------------------------
//--------------------------------------------- erstes gültiges Zeichen zurückgeben ---------------------------------------------------------------

static char spaces(void) {                      //Leerzeichen oder Tab überspringen
  char c;
  while (1) {
    c = *txtpos;
    if (c == SPACE || c == TAB) txtpos++;
    else break;
  }
  return (c);
}

//--------------------------------------------- Unterprogramm - Befehls-und Funktionstabellen lesen -----------------------------------------------

static void scantable(const char *table)
{
  int i = 0;
  table_index = 0;

  while (1)
  {
    // Keine Tabelleneinträge mehr?
    if (pgm_read_byte( table ) == 0)
      return;

    // Passt das Zeichen??
    if (txtpos[i] == pgm_read_byte( table ))
    {
      i++;
      table++;
    }
    else
    {
      //Wort komplett, dann zurück
      if (txtpos[i] + 0x80 == pgm_read_byte( table ))
      {
        txtpos += i + 1;
        spaces();
        return;
      }

      while ((pgm_read_byte( table ) & 0x80) == 0)
        table++;

      // Fortfahren mit dem ersten Zeichen des nächsten Wortes, Positionsindex zurücksetzen
      table++;
      table_index++;
      spaces();
      i = 0;
    }
  }
}


//--------------------------------------------- Unterprogramm - Zahlenausgabe ---------------------------------------------------------------------

void printnum(float num, int modes)   //Ausgabe als float
{ char c[32];
  float tmp;
  int stellen;
  String stz;
  int len;
  unsigned long hexnum;
  String cbuf;

  switch (modes)
  {
    case 0:                                       //normale Zahlenausgabe
      if (num > 9999999 || num < -9999999) {
        printmsg(sci(num, Prezision), 0);         //Ausgabe in Exponential-Schreibweise
      }

      else {
        tmp = num - int(num);                     //Nachkommastelle vorhanden oder 0 ?
        if (tmp == 0) {                           //keine Nachkommastelle
          itoa(num, c, 10);
          printmsg(c, 0);                         //dann Integerausgabe

        }
        else {                                    //Nullen in der Nachkommastelle sollen abgeschnitten werden
          dtostrf(num, 1, Prezision, c);          //Nullen abschneiden
          stz = c;
          len = stz.length();
          stellen = Prezision;
          for (int i = len - 1; i > 0; i--) {
            if ((c[i] > '0') || (c[i] == '.')) break; //keine Null oder komma?
            if (c[i] == '0') stellen -= 1;
          }
          dtostrf(num, 1, stellen, c);                //formatierte Ausgabe ohne Nullen
          printmsg(c, 0);
        }
      }
      break;

    case 1:                                           //Ausgabe als Binärzahl
      hexnum = num;
      outchar('%');
      itoa(num, c, 2);
      printmsg(c, 0);
      Zahlenformat = 0;
      break;

    case 2:                                           //Ausgabe als Hexadezimalzahl
      outchar('#');
    case 3:                                           //Ausgabe als Hexadezimalzahl für Memory_dump ohne #
      hexnum = num;
      itoa(num, c, 16);
      printmsg(c, 0);
      Zahlenformat = 0;
      break;

    default:
      break;
  }//switch(modes)
}

//#######################################################################################################################################
//--------------------------------------------- DUMP - Befehl ---------------------------------------------------------------------------
//#######################################################################################################################################

static int Memory_Dump() {                       //DMP Speichertyp 0..2 <,Adresse>
  int ex = 0, c, was, tpm;
  int ln = (VGAController.getScreenHeight() / y_char[fontsatz]) - 3; //Anzahl Zeilen abhängig vom Fontsatz
  //if (Frame_nr) win_set_cursor(0);               //sind Fenster gesetzt?, dann Hauptfenster setzen
  int x_weite = VGAController.getScreenWidth() / x_char[fontsatz];

#ifdef ILI9341                                  //bei TFT x und y vertauscht
x_weite = (VGAController.getScreenHeight() / x_char[fontsatz]) ;
ln = VGAController.getScreenWidth() / y_char[fontsatz] - 3;    //Anzahl Zeilen abhängig vom Fontsatz
#endif

  byte rdbyte[8];

  word of = FRAM_OFFSET;
  long n;
  long adr = 0;
  was = abs(int(get_value()));                  //nur ganze Zahlen
  if (*txtpos == ',')
  {
    txtpos++;
    adr = abs(get_value());                      //nur ganze Zahlen
  }

  if (*txtpos == 'V') {
    of = 0;                                       //wird V angegeben, kann man den Variablenbereich ansehen
    txtpos++;
  }


  if (was > 2) {
    syntaxerror(syntaxmsg);
    return 1;
  }
  //spi_fram.begin(3);
  while (!ex) {
    for (int i = 1; i < ln; i++)
    {
      if (adr < 0x1000)outchar('0');
      if (adr < 0x100)outchar('0');
      if (adr < 0x10)outchar('0');
      n = adr;
      printnum(adr, 3);                                 //Hexausgabe
      outchar(' ');

      for (int f = 0; f < 8; f++) {                     //8 Speicherplätze lesen und anzeigen
        switch (was) {
          case 1:  //FRAM
            if (spi_fram.read8(of + n) < 16) outchar('0');
            printnum(spi_fram.read8(of + n++), 3);
            if (x_weite > 39) outchar(' ');                       //wenn genug Platz, dann Leerzeichen zwischen den Werten
            break;
          case 2:  //EEPROM
            if (readEEPROM(EEprom_ADDR, n ) < 16) outchar('0');
            printnum(readEEPROM(EEprom_ADDR, n++ ), 3);
            if (x_weite > 39) outchar(' ');
            break;
          default:  //interner RAM
            if (program[int(n)] < 16) outchar('0');
            printnum(program[int(n++)], 3);
            if (x_weite > 39) outchar(' ');
            break;
        }
      }
      if (x_weite < 40) outchar(' ');                             //wenn nicht genug Platz, dann nur ein Leerzeichen nach 8Bytes


      for (int i = 0; i < 8; i++) {
        switch (was) {
          case 1:  //FRAM
            c = spi_fram.read8(of + adr++);//readEEPROM(FRam_ADDR, adr++);
            break;
          case 2:  //EEPROM
            c = readEEPROM(EEprom_ADDR, adr++);
            break;
          default:  //interner RAM
            c = program[int(adr++)];
            break;
        }

        if (c > 31 && c < 127)
          outchar(c);
        else
          outchar('.');
      }
      line_terminator();
    }
    if (wait_key(true) == 3) ex = 1;    //Ctrl-C oder ESC Abbruch

  }//while (ex)
  return 0;
}

//--------------------------------------------- Unterprogramm teste auf gültige Zeilennummer ------------------------------------------------------

static unsigned short testnum(void)               // Überprüfung auf Zeilennummer -> Zeilennummern > 65535 erzeugen einen Überlauf (es fängt wieder bei 1 an)
{
  unsigned int num = 0;
  spaces();

  while (*txtpos >= '0' && *txtpos <= '9' )
  {
    num = num * 10 + *txtpos - '0';
    txtpos++;
  }
  return	num;
}

//--------------------------------------------- Unterprogramm - Fehler/Nachrichtausgabe -----------------------------------------------------------

void printmsg(const char *msg, int nl)
{
  //fbcolor(Vordergrund, Hintergrund);                                //Themen-Farben setzen ist nötig, sonst fällt der Interpreter in die Terminalfarben zurück
  //if (Frame_nr) fbcolor(Frame_vcol[Frame_nr], Frame_hcol[Frame_nr]); //Wenn Fenster, dann Fensterfarben
  while ( pgm_read_byte( msg ) != 0 )
  {
    outchar( pgm_read_byte( msg++ ) );
  }

  if (nl == 1) line_terminator();
}

//--------------------------------------------- Unterprogramm - Tastenabfrage (list-Ausgaben) -----------------------------------------------------

static unsigned short wait_key(bool modes) {
  char c;
  if (modes)
  {
    line_terminator();//Terminal.println();
    printmsg("SPACE<Continue>/CTR+C or ESC<Exit>", 1);
  }
  while (1) {
    if (Terminal.available())
    {
      c = Terminal.read();
      break;
    }
    if (break_marker == true)
    {
      c = 3;
      break_marker == false;
      break;
    }
  }
  return c;
}

//--------------------------------------------- Unterprogramm - Zeile eingeben --------------------------------------------------------------------

static void getln(int m)//char prompt)
{ int chpos = -1;
  if (m) 
  {
    outchar('R');
    outchar('E');
    outchar('A');
    outchar('D');
    outchar('Y');
    outchar('.');
    line_terminator();
  }
  //outchar(prompt);

  txtpos = program_end + sizeof(LINENUM);

  while (1)
  {

    char c = inchar();
    if (c == 27 && Frame_nr) continue;


    switch (c)
    {
      case NL:

      case CR:
        line_terminator();
        // Terminate all strings with a NL
        txtpos[0] = NL;
        return;

      case 0x7F:

        if (txtpos == program_end)
          break;


        if (Frame_nr) {                   //im Fenster kein Backspace, um das Fenster nicht zu beschädigen
          Cursor_x = tc.getCursorCol();
          Cursor_y = tc.getCursorRow();
          tc.setCursorPos(tc.getCursorCol() - 1, Cursor_y);
          tc.setChar(' ');
          tc.setCursorPos(tc.getCursorCol() - 1, Cursor_y);
        }
        else if (chpos > -1) {
          chpos--;
          txtpos--;
          Terminal.write("\b\e[K");      //nicht im Fenster, dann Backspace
        }

        break;
      case 0x03:       // ctrl+c
        line_terminator();
        printmsg(breaks, 1);
        current_line = 0;
        sp = program + sizeof(program);
        txtpos[0] = NL;
        return;
        break;

      default:
        // Wir müssen mindestens ein Leerzeichen lassen, damit wir die Zeile in die richtige Reihenfolge bringen können
        if (txtpos == variables_begin - 2)
          outchar(CTRLH);
        else
        {
          txtpos[0] = c;
          txtpos++;
          chpos++;
          outchar(c);

        }
    }
  }

}


//--------------------------------------------- Unterprogramm - Programmzeile finden ---------------------------------------------------------------
static char *findline(void)
{
  char *line = program_start;
  while (1)
  {
    if (line == program_end)
      return line;

    if (((LINENUM *)line)[0] >= linenum)
      return line;

    // Add the line length onto the current address, to get to the next line;
    line += line[sizeof(LINENUM)];
  }
}


//--------------------------------------------- Unterprogramm - Data-zeile finden -----------------------------------------------------------------

static char *find_data_line(void)
{
  char *line = program_start;
  while (1)
  {
    if (line == program_end)
      return 0;

    dataline = line + sizeof(LINENUM) + sizeof(char);         //Programmzeile übergeben

    if (dataline[0] == 'D' && dataline[1] == 'A' && dataline[2] == 'T' && dataline[3] == 'A')
    {
      data_numbers[num_of_datalines++] = *((LINENUM *)line);
    }
    // Add the line length onto the current address, to get to the next line;
    line += line[sizeof(LINENUM)];
  }
  num_of_datalines -= 1;
  return 0;
}

//--------------------------------------------- Unterprogramm - Grossbuchstabenumwandlung ---------------------------------------------------------

static void toUppercaseBuffer(void)
{
  char *c = program_end + sizeof(LINENUM);
  char quote = 0;

  while (*c != NL)
  {
    // Are we in a quoted string?
    if (*c == quote)
      quote = 0;
    else if (*c == '"' || *c == '\'')
      quote = *c;
    else if (quote == 0 && *c >= 'a' && *c <= 'z')
      *c = *c + 'A' - 'a';
    c++;
  }
}

//--------------------------------------------- Unterprogramm - Zeile ausgeben (Bildschirm oder Datei) --------------------------------------------

int printline(void)
{ int digits = 0;
  int num;
  LINENUM line_num;

  line_num = *((LINENUM *)(list_line));
  list_line += sizeof(LINENUM) + sizeof(char);

  num = line_num;

  printnum(num, 0);

  outchar(' ');
  while (*list_line != NL)
  {
    outchar(*list_line);
    list_line++;
  }

  list_line++;
  line_terminator();
  return line_num;
}

//--------------------------------------------- Unterprogramm - RTC auslesen ----------------------------------------------------------------------

void getdatetime()
{
  DateTime now = rtc.now();           //RTC Funktion
  Zeit[0] = now.hour();
  Zeit[1] = now.minute();
  Zeit[2] = now.second();
  Datum[0] = now.day();
  Datum[1] = now.month();
  Datum[2] = now.year();
  Datum[3] = now.dayOfTheWeek();
  e_rtc.setTime(Zeit[2], Zeit[1], Zeit[0], Datum[0], Datum[1], Datum[2], 0);
}

//--------------------------------------------- Unterprogramm - Hexadezimalzahl in Dezimalzahl konvertieren ---------------------------------------

static int hexDigit(char c)
{
  if (c >= '0' && c <= '9')
    return c - '0';
  if (c >= 'A' && c <= 'F')
    return c - 'A' + 10;
  if (c >= 'a' && c <= 'f')
    return c - 'a' + 10;
  return -1;
}


/*************************************************************************************************************************************************/
//--------------------------------------------- Start - Werteausgabe ------------------------------------------------------------------------------
//--------------------------------------------- Zahlen,Variablen oder Strings auslesen ------------------------------------------------------------
//--------------------------------------------- logische Abhängigkeiten auswerten -----------------------------------------------------------------
//--------------------------------------------- mathematische Funtionen ausführen -----------------------------------------------------------------
/*************************************************************************************************************************************************/
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
void loop()
{

  //--------------------------------------------- hier geht's los -----------------------------------------------------------------------------------
  Basic_Interpreter();
}


//********************************************* Main - Programm ***********************************************************************************


//#################################################################################################################################################
//############################################# Start Basic_Interpreter ###########################################################################
//#################################################################################################################################################

void Basic_Interpreter()
{
  char pa, pb;
  initSD();                                              //SD-Karte initialisieren
  cmd_new();                                             //alles löschen
  print_info();                                          //Start-Bildschirm anzeigen
  check_editor();                                        // befindet sich im EEPROM-Platz 50 die 123, dann die datei tmp.bas automatisch laden
  int a, e;

  //################################################# Hauptprogrammschleife ######################################################
  while (1)
  {

    expression_error = 0;                               //alle Errors zurücksetzen

    if ( triggerRun ) {                                 // AUTO-START-FUNKTION
      triggerRun = false;
      clear_var();                                      //Variablen und Array-Tabelle löschen, Data-Zeiger zurücksetzen
      find_data_line();                                 //Data-Zeilen finden
      current_line = program_start;
      sp = program + sizeof(program);
      goto execline;
    }

    else {
      getln(1);
      //-------------------------------- Start Zeile einfügen ---------------------------------------------
      move_line();                                                  //Zeile in Großbuchstaben umwandeln und ans Ende des Speicher verschieben
      linenum = testnum();                                          // Zeilennummer vorhanden?
      spaces();
      if (linenum == 0) {
        if (direct() == 0) continue;                                //keine Zeilennummer
        else goto interpreteAtTxtpos;                               //Zeile ausführen
      }
      if (insert_line()) {                                          //Zeile in die richtige Position im Speicher einfügen oder löschen, wenn kein Text vorhanden
        continue;
      }
    }
    //------------------------------------------ Ende Zeile einfügen -------------------------------------------------
    continue;


run_next_statement:

    if (run_next() == 1) goto execnextline;

interpreteAtTxtpos:

    if (breakcheck() || break_marker)                                //Programmabbruch mit Ctrl-C oder ESC
    {
      break_marker = false;
      line_terminator();

      if (current_line != NULL)
      {
        printmsg(breakmsg, 0);
        linenum = *((LINENUM *)(current_line));
        printnum(linenum, 0);
        //if(ser_marker) Serial1.print(linenum);
      }

      line_terminator();
      warmstart();
      Terminal.enableCursor(true);                                 //Cursor einschalten
      continue;

    }

    scantable(keywords);                                            //Befehlstabelle scannen
    keyword_index = table_index;


    //####################################################################################################
    //############################### Abarbeitung Befehlstabelle #########################################
    //####################################################################################################

    switch (keyword_index)
    {
      case KW_LIST:                                       // LIST
        list_out();
        continue;
        break;


      case KW_LOAD:                                       // LOAD filename
        if (*txtpos == NL) {
          load_ram();
          continue;
        }

        if (load_file()) {
          continue;
        }
        string_marker = false;
        continue;
        break;

      case KW_NEW:                                        // NEW
        cmd_new();
        continue;
        break;

      case KW_RUN:                                        // RUN
        if (*txtpos == '"') {                             //RUN"/Filename" lädt und startet das Programm
          if (load_file()) {
            continue;
          }
          string_marker = false;
          autorun = true;
        }
        if (*txtpos == '*') {
          load_ram();
        }
        clear_var();
        find_data_line();                                 //Data-Zeilen finden
        current_line = program_start;                     //beginn mit erster Zeile
        sp = program + sizeof(program);
        goto execline;
        break;

      case KW_SAVE:                                       // SAVE filename (/filename.bas)
        if (*txtpos == NL) {
          save_ram();
          continue;
        }
        save_file();
        string_marker = false;
        continue;
        break;

      case KW_NEXT:                                       // NEXT
        goto next;
        break;

      case KW_REN:                                        // RENAME
        expression_error = 0;
        get_value();
        strcpy(filestring, tempstring);       //Tempstring nach filestring kopieren
        if (Test_char(',')) continue;
        get_value();
        renameFile(SD, filestring, tempstring);
        continue;
        break;

      case KW_IF:                                         // IF
        float val;
        logic_counter = 0;
        logica = 0;
        else_marker = false;
        then_marker = true;                               //THEN marker muss noch abgefragt werden (missing_then)
        memset (logic_ergebnis, 0, sizeof (logic_ergebnis));//Logik-Puffer leeren
        expression_error = 0;
        val = get_value();
        logic_ergebnis[logic_counter++] = int(val);       //Ergebnis in Puffer speichern und logicmarker hochzählen
        if (val != 0) {
          val = 0;                                        //für den Fall, das kein AND,OR vorkommt
          break;
        }
        else
        {
          else_marker = true;
          val = 1;                                        //Für den Fall, das es kein AND OR gibt (einfaches IF)
          goto run_next_statement;                        //die ELSE Bedingung muss in der nächsten Zeile stehen
        }
        break;

      case KW_ON:                                         //ON (GOTO/GOSUB)
        ongosub = 0;
        ongosub = get_value();
        if (ongosub == 0) goto execnextline;              //ist der Wert der Variable=0 dann wird mit der nächsten Zeile weitergemacht
        break;

      case KW_GOTO ... KW_GOSUB:                          // GOTO/GOSUB
        expression_error = 0;
        linenum = get_value();
        if (ongosub > 0)
        {
          e = 1;
          while (*txtpos == ',' && e < ongosub)           //so oft wiederholen, wie Zeilennummern existieren
          {
            txtpos++;
            e++;
            linenum = get_value();
          }

          if (a < 0 || a > 65535)
          {
            //syntaxerror(syntaxmsg);
            continue;
          }
        }
        if (keyword_index == KW_GOSUB)
        {
          gosub();
        }

        current_line = findline();
        goto execline;
        break;

      case KW_RETURN:                                     // RETURN
        goto gosub_return;
        break;

      case KW_REM:                                        // REM
        goto execnextline;                                // Ignoriere die komplette Zeile
        break;

      case KW_FOR:
        goto forloop;
        break;

      case KW_INPUT:
        if (input()) continue;
        break;

      case KW_PRINTING:                                   // ?
      case KW_PRINT:                                      // Print
        if (command_Print()) continue;
        break;

      case KW_DOKE:
      case KW_POKE:                                       // POKE adresse,wert
      case KW_FPOKE:
        if (poke(keyword_index)) continue;
        break;

      case KW_DIR:                                        // SD-Card Directory DIR
        cmd_Dir();
        continue;
        break;

      case KW_CHDIR:                                      // SD-Card Change-Directory CD
        cmd_chdir();
        break;

      case KW_MKDIR:                                      // SD-Card Make-Dir MD
        if (cmd_mkdir(1));
        continue;
        break;

      case KW_RMDIR:                                      // SD-Card Remove-Dir RD
        if (cmd_mkdir(0));
        continue;
        break;

      case KW_CLS:                                        // CLS
        if (Frame_nr) {
          win_cls(Frame_nr);
        }
        else {
          tc.setCursorPos(1, 1);
          //cmd_cls();
          GFX.clear();
        }
        break;

      case KW_POS:                                        // POS x,y
        if (set_pos())
          continue;
        break;

      case KW_COLOR:                                      // COLOR v,b
        if (color())
          continue;
        break;

      case KW_PSET:                                       // PSET x,y
        if (pset())
          continue;
        break;

      case KW_CIRCLE:                                     // CIRCLE x,y,w,h,fill
        if (line_rec_circ(1, 4))                          //1=Circle, 0..4 Parameter
          continue;
        break;

      case KW_LINE:                                       // LINE x,y,xx,yy
        if (line_rec_circ(0, 3))                          // 0=Lines, 0..3 Parameter
          continue;
        break;

      case KW_RECT:                                       // RECT x,y,w,h,fill
        if (line_rec_circ(2, 4))                          // 2=Rect, 0..4 Parameter
          continue;
        break;

      case KW_FRAME:                                      // FRAME x,y,w,h,r
        if (line_rec_circ(3, 4))                          // 3=Round, 0..4 Parameter
          continue;
        break;

      case KW_ARC:                                        // ARC x,y,rmin,rmax,gstart,gend,fill
        if (line_rec_circ(4, 6))
          continue;
        break;
      /*
      case KW_BAR:
        if(line_rec_circ(10,5))                           //BAR x, y, orient, w, h, wert
          continue;
        break;
        */
      case KW_SWAP:
        if (line_rec_circ(5, 3))                          //SWAP x,y,xx,yy ->vertauscht vorder und Hintergrundfarbe eines rechtecks
          continue;
        break;

      case KW_COPY:
        if (line_rec_circ(6, 5))                          //Copy x,y,x_dest,y_dest, w, h ->Kopiert ein Rechteck von x,y nach x_dest,y_dest mit der Größe w,h
          continue;
        break;

      case KW_ANGLE:
        if (line_rec_circ(9, 3))
          continue;
        break;

      case KW_FONT:                                       // FONT f
        expression_error = 0;
        val = int(get_value());
        set_font(val);
        break;

      case KW_DELAY:                                       //PAUSE
        expression_error = 0;
        val = get_value();
        delay( val );
        break;

      case KW_END:
        current_line = program_end;
        goto execline;
        break;

      case KW_CLEAR:
        Var_Neu_Platz = 1;                                //auch Array-Ram auf jeden Fall löschen
        clear_var();
        break;

      case KW_THEN:                                      // THEN
        then_marker = false;
        if ( val == 0 ) {                                //Überprüfung, ob alle If Bedingungen war sind
          break;
        }
        else
        {
          else_marker = true;
          goto execnextline;                             //Bedingung nicht erfüllt -> nächste Zeile
        }

      case KW_ELSE:                                       // ELSE
        if (else_marker == true) {
          else_marker = false;
          break;
        }
        goto execnextline;                                //Bedingung nicht erfüllt -> nächste Zeile

      case KW_CURSOR:
        if (cursor_onoff())
          continue;
        break;

      case KW_PREZISION:                                  // PREZ 6 ->Nachkommastellen
        if (set_prezision())
          continue;
        break;

      case KW_DUMP:                                       // DUMP adresse
        if (Memory_Dump())
          continue;
        break;

      case KW_STYLE:
        if (set_style())
          continue;
        break;

      case KW_SCROLL:
        if (line_rec_circ(8, 1))
          continue;
        break;

      case KW_THEME:
        int a;
        a = int(get_value());
        set_theme(a);
        print_info();
        break;

      case KW_DATA:                                       // DATA - wird ignoriert
        goto execnextline;
        break;

      case KW_READ:
        while (1) {
          if (data_get())
          {
            syntaxerror(datamsg);
            continue;
          }
          if (*txtpos == ',')
            txtpos++;
          else break;
        }
        break;

      case KW_RESTORE:                                                //setzen des Datazeigers
        if (*txtpos == NL || *txtpos == ':')                          //wird kein Wert gelesen, datapointer zurücksetzen
        {
          string_marker = false;
          datapointer = 0;
          current_dataline = 0;
        }
        else
        {
          expression_error = 0;                                       //es wird eine Zeilennummer angegeben
          linenum = get_value();
          for (int i = 0; i <= (num_of_datalines - 1); i++)           //scannen, ob Zeilennummer existiert, wenn ja, übernehmen
          {
            if (data_numbers[i] == linenum)
            {
              datapointer = 0;                                       //datapointer zurücksetzen
              current_dataline = i;                                  //Zeiger auf die exitierende Zeile setzen
              break;
            }
          }
        }
        break;

      case KW_DEL:                                        // DEL
        if (cmd_delFiles())
        {
          syntaxerror(notexistmsg);
        }
        continue;
        break;

      case KW_AND:
        expression_error = 0;
        val = get_value();
        logic_ergebnis[logic_counter++] = int(val);       //alle Ergebnisse einlesen und auswerten
        for (int i = 0; i < logic_counter + 1; i++)
        {
          logica += logic_ergebnis[i];
        }
        val = logica - logic_counter;                     //sind alle Bedingungen erfüllt lautet das Ergebnis 0
        break;

      case KW_OR:
        expression_error = 0;
        val = get_value();

        logic_ergebnis[logic_counter++] = int(val);
        for (int i = 0; i < logic_counter + 1; i++)       //alle Ergebnisse einlesen und auswerten
        {
          logica += logic_ergebnis[i];
        }
        val = logica;                                   //ist mindestens eine Bedingung erfüllt lautet das Ergebnis 0 ->war

        if (val == 0)                                   //sind alle Bedingungen falsch wird val auf 1 (falsch gesetzt)
          val = 1;
        else val = 0;                                   //mindestens eine Bedingung ist erfüllt, also -> war
        break;

      case KW_SRTC:                                     //RTC stellen
        if (set_TimeDate())
          continue;
        break;

      case KW_IIC:                                      // I2C Start o. Write o. RequestFrom
        float val1;
        if (Test_char('(')) continue;
        char h;
        h = *txtpos;
        if (h == 'S' || h == 'W' || h == 'Q')
        {
          txtpos += 2;
          expression_error = 0;
          val = get_value();
          if ( h == 'Q') {
            txtpos++;
            expression_error = 0;
            val1 = get_value();
          }
          if (Test_char(')')) continue;

          if ( h == 'S') myI2C.beginTransmission(int(val));           //IIC-Start IIC(S,Adresse)
          else if ( h == 'W') myI2C.write(int(val));                  //IIC-Write IIC(W,Befehl)
          else if ( h == 'Q') myI2C.requestFrom(int(val), int(val1)); //IIC-RequestFrom IIC(Q,Adresse,Anzahl Bytes)
        }
        else {
          continue;
        }
        break;

      case KW_DWRITE:                                   //Port schreiben
        if (set_port())
          continue;
        break;

      case KW_PWM:
        if (set_pwm())
          continue;
        break;

      case KW_DAC:                                        //DAC nur Pin26 - Eingabe in gewünschter Spannung 0-3,3
        if (Test_char('(')) continue;
        expression_error = 0;
        val = get_value();
        if ((val > 3.3) || (val < 0))
        {
          syntaxerror(valmsg);                            //falscher Wert
          continue;
        }
        if (Test_char(')')) continue;
        dacWrite(26, int(val / 0.0129));                  //Wert 0-255 (255= 3.3V 128=1.65V) x=wert/0,0129 (3,3/255)
        break;

      case KW_DRAW:                                       //Draw x,y,0..1
        if (line_rec_circ(7, 2))
          continue;
        break;

      case KW_SPRITE:
        if (Test_char('(')) continue;
        pa = *txtpos;
        if (pa == 'C' || pa == 'D' || pa == 'S') {
          txtpos++;
          if (sprite(pa)) {
            //syntaxerror(syntaxmsg);
            continue;
          }
        }
        else {
          syntaxerror(syntaxmsg);
          continue;
        }
        break;

      case KW_SOUND:
        if (Sound())
          continue;
        break;

      case KW_PULSE:                  //PULSE(PORT,MS)

        if (set_pulse()) {
          //  syntaxerror(syntaxmsg);
          continue;
        }
        break;

      case KW_PEN:

        if (set_pen()) {
          //  syntaxerror(syntaxmsg);
          continue;
        }
        break;


      case KW_LCD:
        if (LCD_Set()) {
          //syntaxerror(syntaxmsg);
          continue;
        }
        break;

      case KW_DEFFUNC:
        if (def_func()) {
          continue;
        }
        break;

      case KW_MCPPORT:
        if (Test_char('(')) continue;
        pa = *txtpos;
        if (pa == 'S' || pa == 'W')  //PORT(S,A/B,0/1)
        {
          txtpos++;
          if (Test_char(',')) continue;
          pb = *txtpos;
          if (pb == 'A' || pb == 'B') {
            txtpos += 2;
          }
          else pb = 'C';

          expression_error = 0;
          val = get_value();
        }

        if (Test_char(')')) continue;
        if (pa == 'S') {
          mcp_Port_direction(pb, int(val));                        //Port AB
        }
        else if (pa == 'W') {
          mcp_Port_write(pb, int(val));
        }

        else {
          continue;
        }
        break;

      case KW_MCPPIN:                                 //Befehl PIN(S/W,Nr,0/1)
        if (Test_char('(')) continue;
        pa = *txtpos;
        txtpos++;
        if (pa == 'S' || pa == 'W')                   //PIN(S/W,Nr,0/1)
        {
          if (Test_char(',')) continue;
          expression_error = 0;
          val = get_value();
          txtpos++;
          expression_error = 0;
          val1 = get_value();
          if (Test_char(')')) continue;
          if (pa == 'S')  mcp_Pin_direction(int(val), int(val1));
          else if (pa == 'W')  mcp_Pin_write(int(val), int(val1));
        }
        else
        {
          continue;
        }
        break;

      case KW_LED:
        if (LED_Set()) {
          //syntaxerror(syntaxmsg);
          continue;
        }
        break;

      case KW_EDIT:
        if (*txtpos == NL) save_tempfile();               //Edit ohne Zeilennummer lädt den Texteditor KILO
        else
        {
          val = int(get_value());                           //Edit <Zeilennummer> startet den Zeileneditor
          Editor(val);
        }
        continue;
        break;

      case KW_BEEP:
        a = 0;
        val = 0;
        if (*txtpos == '(') {
          txtpos++;
          a = get_value();
          if (*txtpos == ',') {
            txtpos++;
            val = get_value();
          }
          if (expression_error) continue;
          if (Test_char(')')) continue;
        }
        Beep(byte(a), val);
        break;

      case KW_DIM:
        if (Array_Dim())
          continue;
        break;

      case KW_OPTION:
        if (Option())
          continue;
        break;

      case KW_MOUNT:
        initSD();                                              //SD-Karte initialisieren
        break;

      case KW_COM:
        if (cmd_serial())
          continue;
        break;

      case KW_PIC:
        if (show_Pic())
          continue;
        break;

      case KW_OPEN:
        file_rw_open();
        break;

      case KW_CLOSE:
        Datei_open = false;
        File_pos = 0;
        File_size = 0;
        break;

      case KW_FILE:                 //File_Open,File_Read,File_Write,File_Close
        File_Operations();
        break;

      case KW_TYPE:
        type_file();
        break;

      case KW_GRID:
        if (make_grid())
          continue;
        break;

      case KW_TEXT:
        if (draw_text())
          continue;
        break;

      case KW_WINDOW:
        if (win())
          continue;
        break;

      case KW_HELP:
        if (*txtpos == NL) show_help();
        else show_help_name();
        *txtpos = NL;                     //Zeile muss beendet werden,da bei Eingabe des Befehls nach Help sonst Fehler auftreten (es werden evt. Parameter erwartet)
        break;

      case KW_DEFAULT:
        if (var_get())
          continue;
        break;


      default:

        break;

    } //switch(table_index)


    goto run_next_statement;

    //################################### Ende der Befehlstabelle #########################################

execnextline:
    if (current_line == NULL)   // Processing direct commands?
      continue;
    current_line +=  current_line[sizeof(LINENUM)];

execline:
    if (current_line == program_end) { // Out of lines to run
      warmstart();
      continue;
    }

    //----------------------- TRON-Funktion --------------------------------------
    if (tron_marker) {
      Terminal.print('<' + String(*((LINENUM *)(current_line))) + '>');
    }
    //----------------------------------------------------------------------------

    txtpos = current_line + sizeof(LINENUM) + sizeof(char);
    goto interpreteAtTxtpos;


forloop:
    {

      //char var, c, d;
      float initial, step, to_var;
      int var, c, d, z;
      z = 0;
      c = spaces();
      if (c < 'A' || c > 'Z')
      {
        syntaxerror(syntaxmsg);
        continue;
      }
      var = int(c - 'A');
      *txtpos++;
      d = int(spaces());

      if (d >= 'A' && d <= 'Z')
      { c = (d - 'A' + 1) * 26;
        var = var + c;
        *txtpos++;

      }
      if (Test_char('=')) continue;
      spaces();

      initial = get_value();
      if (expression_error) continue;

      scantable(to_tab);
      if (table_index != 0)
      {
        syntaxerror(syntaxmsg);
        continue;
      }

      to_var = get_value();
      if (expression_error) continue;

      scantable(step_tab);
      if (table_index == 0)
      {
        step = get_value();
        if (expression_error) continue;
      }
      else
        step = 1;
      c = spaces();

      if (c != NL && c != ':')
      {
        syntaxerror(syntaxmsg);
        continue;
      }

      if (!expression_error && (*txtpos == NL || *txtpos == ':'))
      {
        string_marker = false;
        struct stack_for_frame *f;
        if (sp + sizeof(struct stack_for_frame) < stack_limit) {
          printmsg(fornextmsg, 1);
          printnum(linenum, 0);

          //if(ser_marker) Serial1.print(linenum,DEC);
          warmstart();
          continue;
        }

        sp -= sizeof(struct stack_for_frame);
        f = (struct stack_for_frame *)sp;
        ((float *)variables_begin)[var] = initial;// - 'A'];

        f->frame_type = STACK_FOR_FLAG;
        f->for_var  = var;
        f->to_var   = to_var;
        f->step     = step;
        f->txtpos   = txtpos;
        f->current_line = current_line;
        goto run_next_statement;
      }

    }

    //syntaxerror(syntaxmsg);
    //continue;


next:
    // Fnd the variable name
    spaces();

    if (*txtpos < 'A' || *txtpos > 'Z')
    {
      printmsg(fornextmsg, 1);
      continue;
    }

    txtpos++;
    spaces();

gosub_return:
    // Now walk up the stack frames and find the frame we want, if present
    tempsp = sp;
    while (tempsp < program + sizeof(program) - 1)
    {
      switch (tempsp[0])
      {
        case STACK_GOSUB_FLAG:
          if (table_index == KW_RETURN)
          {
            struct stack_gosub_frame *f = (struct stack_gosub_frame *)tempsp;
            current_line  = f->current_line;
            txtpos      = f->txtpos;
            sp += sizeof(struct stack_gosub_frame);
            if (ongosub == 0)
            {
              goto run_next_statement;   //nur Gosub führt nach dem Return den nächsten Befehl in der Zeile aus
            }
            else {
              goto execnextline;       //bei on gosub wird nach dem Return in die nächste Zeile gesprungen
            }
          }
          // This is not the loop you are looking for... so Walk back up the stack
          tempsp += sizeof(struct stack_gosub_frame);
          break;
        case STACK_FOR_FLAG:
          // Flag, Var, Final, Step
          if (table_index == KW_NEXT)
          { int tmp;
            struct stack_for_frame *f = (struct stack_for_frame *)tempsp;
            // Is the the variable we are looking for?

            if (txtpos[-1] >= 'A' && txtpos[-1] <= 'Z') //== f->for_var)          //erster Variablenbuchstabe
            {
              int ef, xf;
              tmp = int(txtpos[-1] - 'A');


              if (*txtpos >= 'A' && *txtpos <= 'Z') //txtpos[0] == f -> for_var)   //zweiter Variablenbuchstabe
              {
                ef = int(*txtpos - 'A' + 1) * 26;
                tmp = tmp + ef;
                txtpos++;
              }

              //Terminal.println(*txtpos,DEC);
              if (tmp == f->for_var)
              {
                float *varaddr = ((float *)variables_begin) + tmp;//txtpos[-1] - 'A';

                *varaddr = *varaddr + f->step;
                // Use a different test depending on the sign of the step increment
                if ((f->step > 0 && *varaddr <= f->to_var) || (f->step < 0 && *varaddr >= f->to_var))
                {
                  // We have to loop so don't pop the stack
                  txtpos = f->txtpos;
                  current_line = f->current_line;
                  goto run_next_statement;
                }
                // We've run to the end of the loop. drop out of the loop, popping the stack
                sp = tempsp + sizeof(struct stack_for_frame);
                goto run_next_statement;
              }
            }
          }
          // This is not the loop you are looking for... so Walk back up the stack
          tempsp += sizeof(struct stack_for_frame);
          break;
        default:
          warmstart();
          continue;
      }
    }
    // Didn't find the variable we've been looking for

    syntaxerror(syntaxmsg);
    //continue;

  }//while(1)
} //Basic_interpreter

//#################################################################################################################################################
//############################################# Ende Basic_Interpreter ############################################################################
//#################################################################################################################################################





//#######################################################################################################################################
//--------------------------------------------- PRINT - Befehl --------------------------------------------------------------------------
//#######################################################################################################################################
static int command_Print(void)
{
  int k = 0;
  int xp, yp;

  while (!k)
  { char c = spaces();

    switch (c)
    {

      case ';':
        semicolon = true;
        if (skip_spaces() == NL)
        {
          k = 1;
        }
        break;

      case '"':
        print_quoted_string();
        break;

      case ':':
        if (!semicolon) line_terminator();
        txtpos++;
        k = 1;
        semicolon = false;
        break;

      case NL:
        line_terminator();
        semicolon = false;
        k = 1;
        break;

      case ',':
        xp = tc.getCursorCol();             //Tabulator ausgeben
        yp = tc.getCursorRow();
        if (xp < 37)
          tc.setCursorPos(xp + 8, yp);
        else {
          line_terminator();
        }
        semicolon = true;
        if (skip_spaces() == NL)
        {
          k = 1;
        }
        break;

      case 'A':                             //Print AT(x,y);
        tmptxtpos = txtpos;
        txtpos++;
        if (*txtpos == 'T')
        {
          txtpos++;
          if (*txtpos == '(')
          {
            txtpos++;
            xp = get_value();
            if (*txtpos == ',')
            {
              txtpos++;
              yp = get_value();
              tc.setCursorPos(xp, yp);
              if (*txtpos != ')') k = 2;
              else {
                txtpos++;
                break;
              }
            }
            else k = 2;
          }
          else  txtpos = tmptxtpos; //wenn nach AT keine Klammer kommt kann es sich um die Funktion ATN(x) handeln

        }
        else {
          txtpos = tmptxtpos;
        }

      default:
        float e;

        e = get_value();                    //Zahl oder Variable lesen

        if (expression_error) k = 2;
        if (func_string_marker == true) {
          for (int i = 0; i < fstring; i++) {
            printmsg(tempstring, 0);
          }
          func_string_marker = false;
          string_marker = false;
          chr = false;
        }
        else if (string_marker == true)                  //String?
        {
          printmsg(tempstring, 0);
          func_string_marker = false;
          string_marker = false;
          chr = false;
        }
        else if (chr == true)
        {
          outchar(int(e));
          chr = false;                       //marker zurücksetzen
          string_marker = false;
        }
        else if (tab_marker == true)         //TAB und SPC-Funktion
        {
          tab_marker = false;                //marker zurücksetzen
        }
        else {
          printnum(e, Zahlenformat);         //Zahl
        }
    }


  }//while(!k)

  if (k == 2)
    return 1;                               //Fehler - wieder von vorn

  return 0;                                 // nächster Befehl
}

//#######################################################################################################################################
//--------------------------------------------- Variablen - Eingabe ---------------------------------------------------------------------
//#######################################################################################################################################

static float var_get(void)
{
  float value;
  float *var;
  //char *st;
  int tmp, stmp, i, var_pos, array_art ;
  char c;
  word arr_adr;

  array_art = 0;

  if (*txtpos < 'A' || *txtpos > 'Z')                                     //erster Variablenbuchstabe
  {
    syntaxerror(syntaxmsg);
    return 1;
  }
  var_pos = *txtpos - 'A';
  var = (float *)variables_begin + var_pos;
  stmp = (int) (*txtpos - 'A') * STR_LEN;                                //Strings nur als einbuchstabige Variablen erlaubt, deshalb Variablenadresse sichern
  txtpos++;
  if (*txtpos >= 'A' && *txtpos <= 'Z') {                            //zweiter Variablenbuchstabe
    tmp = (int) ((*txtpos - 'A' + 1) * 26);
    var = var + tmp;
    txtpos++;
  }

  //------------------------------------------------------------------------------------------------------------------------------------------------------------
  while (*txtpos >= 'A' && *txtpos <= 'Z') txtpos++;  //so sind auch lange Variablennamen möglich ->siehe auch expr4()
  //------------------------------------------------------------------------------------------------------------------------------------------------------------
  if (*txtpos == '(') {
    txtpos++;
    expression_error = 0;
    arr_adr = rw_array(var_pos, VAR_TBL);                                  //numerische Array? Adresse im Zahlen-Arrayfeld
    if (expression_error) return 1;                                        //Fehler? dann zurück
    array_art = 1;
  }
  else if (*txtpos == '$')
  { //String?
    txtpos++;

    if (*txtpos == '(') {                                                 //kommt eine Klammer vor, muss es sich um ein Array handeln
      txtpos++;
      expression_error = 0;
      arr_adr = rw_array(var_pos, STR_TBL);                               //String_array?, Adresse im String-Arrayfeld
      if (expression_error) return 1;                                     //Fehler? dann zurück
      array_art = 2;
    }

    if (Test_char('=')) return 1;                                         //Test auf '='

    get_value();                                                         //Stringvariable?, Zeichenkette oder numerische Variable

    i = 0;
    while (1)
    {
      c = tempstring[i];
      if (c == '\0') {
        if (array_art == 2) {
          SPI_RAM_write8(arr_adr + i, '\0');
        }
        else {
          Stringtable[stmp + i] = '\0';                                   //Nullterminator setzen
        }
        break;
      }
      else {
        if (i < STR_LEN) {
          if (array_art == 2) {
            SPI_RAM_write8(arr_adr + i++, c);
          }
          else Stringtable[stmp + i++] = c;
        }
        else {
          if (array_art == 2) {
            SPI_RAM_write8(arr_adr + i, '\0');
            break;
          }
          else {
            Stringtable[stmp + i] = '\0';
            break;
          }
        }
      }
    }
    return 0;
  }// Ende String?

  if (Test_char('='))
    return 1;


  spaces();
  value = get_value();
  if (expression_error) return 1;//continue;

  // Check that we are at the end of the statement
  if (*txtpos != NL && *txtpos != ':')
  {
    syntaxerror(syntaxmsg);
    return 1;

  }

  if (array_art == 1) {
    byte* bytes = (byte*)&value;                            //float nach byte-array umwandeln
    SPI_RAM_write(arr_adr, bytes, 4);
    return 0;
  }

  *var = value;
  return 0;
}

float rw_array(int num, word table) {
  int x, y, z, xx, yy, zz;    //Dimensionswerte aus der Klammer lesen
  word vadresse, ort;
  byte p_data[8], len;        //Dimensionswerte im FRAM
  x = y = z = 0;

  x = get_value();            //erste Dimension
  if (*txtpos == ',') {
    txtpos++;
    y = get_value();          //eventuelle zweite Dimension
  }
  if (*txtpos == ',') {
    txtpos++;
    z = get_value();          //eventuelle dritte Dimension
  }
  if (Test_char(')')) {
    expression_error = 1;
    return 0;
  }

  ort = table + (num * 8);                                         //1=num.Var-Position der Array-Dimension in Array-Tabelle (A=0, B=1, C=2 usw.)
  if (table == VAR_TBL) len = sizeof (float);                        //Eintragslänge bei float 4
  else if (table == STR_TBL) len = STR_LEN;

  //Dimensionswerte aus dem FRAM lesen und mit Eingabe vergleichen
  spi_fram.read(ort, p_data, 6);
  //readBuffer(FRam_ADDR, ort, 6, p_data);

  vadresse = word(p_data[0], p_data[1]);                                //word(h, l) //vadresse = p_data[0] << 8; vadresse += p_data[1]; Variablen-Feldadresse - Adresse bei dem das Array-Feld beginnt
  xx = word (p_data[2], p_data[3]);                                     //1.Dimension
  yy = p_data[4];                                                       //2.Dimension
  zz = p_data[5];                                                       //3.Dimension

  if (x > xx || y > yy || z > zz) {                                     //Dimensionsfehler entdeckt
    expression_error = 1;
    syntaxerror(dimmsg);
    return 0;
  }
  ort = vadresse + ((xx + 1) * y * len) + (x * len) + ((xx + 1) * (yy + 1) * len * z);
  return ort;
}

//--------------------------------------------- Variablen löschen ---------------------------------------------------------------------------------

void clear_var()
{
  long w_ert = 0;
  byte* bytes = (byte*)&w_ert;

  memset(tempstring, '\0', sizeof(tempstring));

  for (int i = 0; i < VAR_SIZE * 26 * 27; i++)                     //Variablen löschen
  {
    variables_begin[i] = 0;
  }
  memset(Stringtable, '\0', sizeof(Stringtable));
  //for (int i = 0; i < 0x0fff; i += 4) SPI_RAM_write(i, bytes, 4);
  if (Var_Neu_Platz > 0) {                                          //SPI-Ram nur löschen, wenn Arrays definiert wurden
    SPI_RAM_fill(0x0, 0x0fff, 0);                                   //die ersten 4kb Array-Variablen im Ram löschen
    SPI_RAM_fill(0x7e00, 0x8000, 0);                                //Array-Tabellen löschen
  }

  //for (int i = 0x7e00; i < 0x8000; i += 4) SPI_RAM_write(i, bytes, 4);
  Var_Neu_Platz = 0;                                               //Array-Zeiger zurücksetzen
  num_of_datalines = 0;                                            //Datazeilenzähler zurücksetzen
  del_window();                                                    //Fensterparameter löschen
  Frame_nr = 0;                                                    //Hauptfenster setzen
  return;
}

//#######################################################################################################################################
//--------------------------------------------- NEW-Befehl ------------------------------------------------------------------------------
//#######################################################################################################################################
void cmd_new(void) {
  long w_ert = 0;
  byte* bytes = (byte*)&w_ert;
  program_start = program;
  program_end = program_start;
  sp = program + sizeof(program);                                     // Needed for printnum

  stack_limit = program + sizeof(program) - STACK_SIZE;               // - ARRAY_SIZE;
  variables_begin = stack_limit - (26 * 27 * VAR_SIZE) ;              //26*27 (2)Buchstaben als Variablen
  memset(program, 0, 1000);                                           //die ersten 1000 Bytes des Speichers löschen
  clear_var();                                                        //Variablen und Array-Tabelle löschen
}

//#######################################################################################################################################
//--------------------------------------------- THEME - Befehl --------------------------------------------------------------------------
//#######################################################################################################################################

static int set_theme(int value)
{
  //int fn;

  switch (value)
  {
    case 0: //C64
      Vordergrund = 43;
      Hintergrund = 18;
      set_font(25);
      break;

    case 1: //C128
      Vordergrund = 46;
      Hintergrund = 21;
      set_font(25);
      break;

    case 2: //CPC
      Vordergrund = 60;
      Hintergrund = 1;
      set_font(19);
      break;

    case 3: //ATARI-800
      Vordergrund = 26;
      Hintergrund = 5;
      set_font(21);
      break;

    case 4: //ZX-SPECTRUM
      Vordergrund = 0;
      Hintergrund = 42;
      set_font(22);
      break;

    case 5: //KC87
      Vordergrund = 63;
      Hintergrund = 0;
      set_font(22);
      break;

    case 6: //KC 85
      Vordergrund = 63;
      Hintergrund = 2;
      set_font(19);
      break;

    case 7: //VIC20
      Vordergrund = 2;
      Hintergrund = 63;
      set_font(2);
      break;

    case 8: //TRS80
      Vordergrund = 0;
      Hintergrund = 24;
      set_font(22);
      break;

    case 9: //TI-99
      Vordergrund = 0;
      Hintergrund = 30;
      set_font(22);
      break;

    case 10:    //LCD
      Vordergrund = 20;
      Hintergrund = 41;
      set_font(3);
      break;

    default:
      Vordergrund = user_vcolor;
      Hintergrund = user_bcolor;
      fontsatz = user_font;
      set_font(fontsatz);
      value = 11;
      break;
  }
  fbcolor(Vordergrund, Hintergrund);
  tc.setCursorPos(1, 1);
  GFX.clear();
  Theme_state = value;
  return 0;
}

//--------------------------------------------- Unterprogramm - Überprüfung auf Zeichen -----------------------------------------------------------

static int Test_char(char az)
{

  // check for char az
  if (*txtpos != az)
  {
    syntaxerror(syntaxmsg);
    return 1;
  }
  txtpos++;
  spaces();
  return 0;
}

//#######################################################################################################################################
//--------------------------------------------- POKE - Befehl ---------------------------------------------------------------------------
//#######################################################################################################################################

static int poke(int fn)             //POKE WAS,ADRESSE,WERT
{
  unsigned long address, wert;
  float w_ert;
  int was, weite;
  byte value, p_data[2];

  was = abs(get_value());                                       //Speicherort 0..2 ->0-RAM, 1-FRAM, 2-EEPROM
  if (was > 2) was = 2;
  if (Test_char(',')) return 1;

  address = abs(get_value());                                  //Speicheradresse
  if (Test_char(',')) return 1;

  if (fn == KW_FPOKE) {
    w_ert = get_value();                                        //floatwert poken
    goto next;
  }

  wert = abs(get_value());                                     //zu speichernder Wert
  if (*txtpos != ',') weite = 1;                               //wenn kein Komma,dann Byte
  else
    weite = abs(get_value());                                  //byte, word ->1,2

next:
  // Testen auf Zeilenende oder ':'
  if (*txtpos != NL && *txtpos != ':')
  {
    syntaxerror(syntaxmsg);
    return 1;
  }
  //---------------------------- RAM -----------------------------------------------
  if (was == 0) {
    if (fn == KW_POKE)  program[address] = byte(wert);            //RAM  Byte
    else if (fn == KW_DOKE)
    {
      program[address] = highByte(wert);                          //RAM  Word
      program[address + 1] = lowByte(wert);                       //RAM
    }
    else if (fn == KW_FPOKE) {
      byte* bytes = (byte*)&w_ert;
      program[address] = byte(bytes[0]);
      program[address + 1] = byte(bytes[1]);
      program[address + 2] = byte(bytes[2]);
      program[address + 3] = byte(bytes[3]);
    }
    return 0;
  }
  //---------------------------- FRAM ---------------------------------------------
  else if (was == 1) {
    if (fn == KW_POKE)  SPI_RAM_write8(FRAM_OFFSET + address, byte(wert));   //FRAM Byte
    else if (fn == KW_DOKE)
    {
      p_data[0] = highByte(wert);
      p_data[1] = lowByte(wert);
      SPI_RAM_write(FRAM_OFFSET + address, p_data, 2);                       //FRAM Word
    }
    else if (fn == KW_FPOKE) {
      byte* bytes = (byte*)&w_ert;
      SPI_RAM_write(FRAM_OFFSET + address, bytes, 4);                        //FRAM float
    }
    return 0;
  }
  //----------------------------- EEPROM -------------------------------------------
  else if (fn == KW_POKE)  writeEEPROM(EEprom_ADDR, address, byte(wert));   //EEPROM Byte
  else if (fn == KW_DOKE)
  {
    p_data[0] = highByte(wert);
    p_data[1] = lowByte(wert);
    WriteBuffer(EEprom_ADDR, address, 2, p_data);                           //EEPROM Word
  }
  else if (fn == KW_FPOKE) {                                                //EEPROM float
    byte* bytes = (byte*)&w_ert;
    WriteBuffer(EEprom_ADDR, address, 4, bytes);
  }
  return 0;

}

//#######################################################################################################################################
//--------------------------------------------- STYLE - Befehl --------------------------------------------------------------------------
//#######################################################################################################################################

static int set_style(void)
{
  int st;

again:
  expression_error = 0;
  st = abs(int(get_value()));         //nur ganze Zahlen
  if (expression_error) return 1;

  switch (st) {
    case 0: Terminal.print("\e[0m");                          //normal
      break;
    case 1: Terminal.print("\e[1m");                          //bold
      break;
    case 2: Terminal.print("\e[3m");                          //italic
      break;
    case 3: Terminal.print("\e[4m");                          //underline
      break;
    case 4: Terminal.print("\e[7m");                          //invers
      break;
    case 5: Terminal.print("\e[5m");                          //blink
      break;
    case 6: Terminal.print("\e#6");                           //float width
      break;

    default:
      break;
  }
  if (spaces() == ',')                                        //weitere Style-Parameter? dann wieder von vorn
  {
    txtpos++;
    goto again;
  }
  return 0;
}


//#######################################################################################################################################
//--------------------------------------------- Lines/CIRCLE/RECT - Befehl --------------------------------------------------------------
//#######################################################################################################################################
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
