Zille9/ESP32-Basic/Software/Altair8800/src/machine.cpp

/*
  Created by Fabrizio Di Vittorio (fdivitto2013@gmail.com) - <http://www.fabgl.com>
  Copyright (c) 2019-2022 Fabrizio Di Vittorio.
  All rights reserved.


* Please contact fdivitto2013@gmail.com if you need a commercial license.


* This library and related software is available under GPL v3.

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
  You should have received a copy of the GNU General Public License
  along with FabGL.  If not, see <http://www.gnu.org/licenses/>.
 */



#include <stdio.h>
#include <stdint.h>
#include <string.h>
#include <sys/stat.h>

#include "machine.h"

#include "fabgl.h"
#include "fabutils.h"







// Altair 88-DSK Boot ROM (starts at 0xFF00)
const uint8_t Altair88DiskBootROM[256] = {
  0x21, 0x00, 0x4c, 0x11, 0x18, 0xff, 0x0e, 0xe6, 0x1a, 0x77, 0x13, 0x23,
  0x0d, 0xc2, 0x08, 0xff, 0xc3, 0x00, 0x4c, 0x00, 0x00, 0x00, 0x00, 0x00,
  0xf3, 0x31, 0x62, 0x4d, 0xaf, 0xd3, 0x08, 0x3e, 0x04, 0xd3, 0x09, 0xc3,
  0x19, 0x4c, 0xdb, 0x08, 0xe6, 0x02, 0xc2, 0x0e, 0x4c, 0x3e, 0x02, 0xd3,
  0x09, 0xdb, 0x08, 0xe6, 0x40, 0xc2, 0x0e, 0x4c, 0x11, 0x00, 0x00, 0x06,
  0x00, 0xdb, 0x08, 0xe6, 0x04, 0xc2, 0x25, 0x4c, 0x3e, 0x10, 0xf5, 0xd5,
  0xc5, 0xd5, 0x11, 0x86, 0x80, 0x21, 0xd4, 0x4c, 0xdb, 0x09, 0x1f, 0xda,
  0x38, 0x4c, 0xe6, 0x1f, 0xb8, 0xc2, 0x38, 0x4c, 0xdb, 0x08, 0xb7, 0xfa,
  0x44, 0x4c, 0xdb, 0x0a, 0x77, 0x23, 0x1d, 0xca, 0x5a, 0x4c, 0x1d, 0xdb,
  0x0a, 0x77, 0x23, 0xc2, 0x44, 0x4c, 0xe1, 0x11, 0xd7, 0x4c, 0x01, 0x80,
  0x00, 0x1a, 0x77, 0xbe, 0xc2, 0xc1, 0x4c, 0x80, 0x47, 0x13, 0x23, 0x0d,
  0xc2, 0x61, 0x4c, 0x1a, 0xfe, 0xff, 0xc2, 0x78, 0x4c, 0x13, 0x1a, 0xb8,
  0xc1, 0xeb, 0xc2, 0xb5, 0x4c, 0xf1, 0xf1, 0x2a, 0xd5, 0x4c, 0xd5, 0x11,
  0x00, 0xff, 0xcd, 0xce, 0x4c, 0xd1, 0xda, 0xbe, 0x4c, 0xcd, 0xce, 0x4c,
  0xd2, 0xae, 0x4c, 0x04, 0x04, 0x78, 0xfe, 0x20, 0xda, 0x2c, 0x4c, 0x06,
  0x01, 0xca, 0x2c, 0x4c, 0xdb, 0x08, 0xe6, 0x02, 0xc2, 0xa0, 0x4c, 0x3e,
  0x01, 0xd3, 0x09, 0xc3, 0x23, 0x4c, 0x3e, 0x80, 0xd3, 0x08, 0xc3, 0x00,
  0x00, 0xd1, 0xf1, 0x3d, 0xc2, 0x2e, 0x4c, 0x3e, 0x43, 0x01, 0x3e, 0x4f,
  0x01, 0x3e, 0x4d, 0x47, 0x3e, 0x80, 0xd3, 0x08, 0x78, 0xd3, 0x01, 0xc3,
  0xc9, 0x4c, 0x7a, 0xbc, 0xc0, 0x7b, 0xbd, 0xc9, 0x84, 0x00, 0x4c, 0x24,
  0x16, 0x56, 0x16, 0x00, 0x00, 0x00, 0x00, 0x00, 0x00, 0x00, 0x00, 0x00,
  0x00, 0x00, 0x00, 0x00
};




////////////////////////////////////////////////////////////////////////////////////
// buffered file IO routines

///*
FILE * bufferedFile                = nullptr;
uint8_t * bufferedFileData         = nullptr;
int bufferedFileDataPos            = -1; // position of bufferedFileData related to the actual file
bool bufferedFileChanged           = false;
constexpr int bufferedFileDataSize = 4388;//4388;


void diskFlush(FILE * file = nullptr)
{
  // flush bufferedFile
  if (bufferedFileChanged && bufferedFile && bufferedFileDataPos != -1) {
    fseek(bufferedFile, bufferedFileDataPos, SEEK_SET);
    //fprintf(stderr, "fseek(%d) fwrite(%d)\n", bufferedFileDataPos, bufferedFileDataSize);
    fwrite(bufferedFileData, bufferedFileDataSize, 1, bufferedFile);
    fflush(bufferedFile);
    fsync(fileno(bufferedFile));  // workaround from forums...
    bufferedFileChanged = false;
  }
  if (file) {
    // flush specified file
    fflush(file);
    fsync(fileno(file));  // workaround from forums...
  }
}


// size cannot be > Mits88Disk::SECTOR_SIZE
void fetchFileData(FILE * file, int position, int size)
{
  if (bufferedFileData == nullptr)
    bufferedFileData = new uint8_t[bufferedFileDataSize];
  if (bufferedFile != file) {
    diskFlush();
    bufferedFileDataPos = -1;
    bufferedFile = file;
  }
  if (bufferedFileDataPos == -1 || position < bufferedFileDataPos || position + size >= bufferedFileDataPos + bufferedFileDataSize) {
    diskFlush();
    fseek(file, position, SEEK_SET);
    //fprintf(stderr, "fseek(%d) fread(%d)\n", position, bufferedFileDataSize);
    fread(bufferedFileData, bufferedFileDataSize, 1, file);
    bufferedFileDataPos = position;
  }
}


// size cannot be > Mits88Disk::SECTOR_SIZE
void diskRead(int position, void * buffer, int size, FILE * file)
{
  fetchFileData(file, position, size);
  memcpy(buffer, bufferedFileData + position - bufferedFileDataPos, size);
}


// size cannot be > Mits88Disk::SECTOR_SIZE
void diskWrite(int position, void * buffer, int size, FILE * file)
{
  fetchFileData(file, position, size);
  memcpy(bufferedFileData + position - bufferedFileDataPos, buffer, size);
  bufferedFileChanged = true;
}
//*/


/*

// NO BUFFERING

void diskRead(int position, void * buffer, int size, FILE * file)
{
  fseek(file, position, SEEK_SET);
  fread(buffer, size, 1, file);
}


void diskWrite(int position, void * buffer, int size, FILE * file)
{
  fseek(file, position, SEEK_SET);
  fwrite(buffer, size, 1, file);
}

void diskFlush(FILE * file = nullptr)
{
  fflush(file);
  fsync(fileno(file));  // workaround from forums...
}

//*/




////////////////////////////////////////////////////////////////////////////////////
// Machine


Machine::Machine()
  : m_devices(nullptr),
    m_realSpeed(false),
    m_menuCallback(nullptr)
{
  m_Z80.setCallbacks(this, readByte, writeByte, readWord, writeWord, readIO, writeIO);
  m_i8080.setCallbacks(this, readByte, writeByte, readWord, writeWord, readIO, writeIO);
}


Machine::~Machine()
{
  delete [] m_RAM;
}


void Machine::attachDevice(Device * device)
{
  device->next = m_devices;
  m_devices = device;
}


void Machine::load(int address, uint8_t const * data, int length)
{
  for (int i = 0; i < length; ++i)
    m_RAM[address + i] = data[i];
}


void Machine::attachRAM(int RAMSize)
{
  m_RAM = new uint8_t[RAMSize];
}


int Machine::nextStep(CPU cpu)
{
  return (cpu == CPU::i8080 ? m_i8080.step() : m_Z80.step());
}


void Machine::run(CPU cpu, int address)
{
  if (cpu == CPU::i8080) {
    m_i8080.reset();
    m_i8080.setPC(address);
  } else {
    m_Z80.reset();
    m_Z80.setPC(address);
  }

  constexpr int timeToCheckKeyboardReset = 200000;
  int timeToCheckKeyboard = timeToCheckKeyboardReset;

  while (true) {
    int cycles = 0;
    if (m_realSpeed) {
      int64_t t = esp_timer_get_time();  // time in microseconds
      cycles = nextStep(cpu);
      if (m_realSpeed) {
        t += cycles / 2;                 // at 2MHz each cycle last 0.5us, so instruction time is cycles*0.5, that is cycles/2
        while (esp_timer_get_time() < t)
          ;
      }
    } else {
      cycles = nextStep(cpu);
    }
    for (Device * d = m_devices; d; d = d->next)
      d->tick(cycles);

    // time to check keyboard for menu key (F9 or PAUSE)?
    timeToCheckKeyboard -= cycles;
    if (timeToCheckKeyboard < 0) {
      timeToCheckKeyboard = timeToCheckKeyboardReset;
      auto keyboard = fabgl::PS2Controller::keyboard();
      if (m_menuCallback && (keyboard->isVKDown(VirtualKey::VK_PAUSE) || keyboard->isVKDown(VirtualKey::VK_F9)))
        m_menuCallback();
    }
  }

}


int Machine::readByte(void * context, int address)
{
  return ((Machine*)context)->m_RAM[address];
}


void Machine::writeByte(void * context, int address, int value)
{
  ((Machine*)context)->m_RAM[address] = value;
}


int Machine::readIO(void * context, int address)
{
  auto m = (Machine*)context;
  for (Device * d = m->m_devices; d; d = d->next) {
    int value;
    if (d->read(address, &value))
      return value;
  }

  // not handlded!

  //Serial.printf("readIO 0x%x\n\r", address);

  return 0xff;
}


void Machine::writeIO(void * context, int address, int value)
{
  auto m = (Machine*)context;
  for (Device * d = m->m_devices; d; d = d->next)
    if (d->write(address, value))
      return;

  // not handlded!

  //Serial.printf("writeIO 0x%x %d %c\n\r", address, value, (char)value);
}


// Machine
////////////////////////////////////////////////////////////////////////////////////



////////////////////////////////////////////////////////////////////////////////////
// SIO


SIO::SIO(Machine * machine, int address)
  : Device(machine),
    m_address(address),
    m_stream(nullptr)
{
  machine->attachDevice(this);
}


void SIO::attachStream(Stream * value)
{
  m_stream = value;
}


bool SIO::read(int address, int * result)
{
  if (address == m_address) {
    // CTRL
    bool available = false;
    if (m_stream)
      available = m_stream->available();
    *result = 0b10 | (available ? 1 : 0);
    return true;
  } else if (address == m_address + 1) {
    // DATA
    int ch = 0;
    if (m_stream && m_stream->available())
      ch = m_stream->read();
    *result = ch;
    return true;
  }
  return false;
}


bool SIO::write(int address, int value)
{
  if (address == m_address) {
    // CTRL
    return true;
  } else if (address == m_address + 1) {
    // DATA
    if (m_stream)
      m_stream->write(value);
    //fprintf(stderr, "SIO: %c\n", value);
    return true;
  }
  return false;
}

// SIO
////////////////////////////////////////////////////////////////////////////////////




////////////////////////////////////////////////////////////////////////////////////
// Mits88Disk disk drive controller


Mits88Disk::Mits88Disk(Machine * machine, DiskFormat diskFormat)
  : Device(machine),
    m_tick(0),
    m_diskFormat(diskFormat),
    m_drive(-1),
    m_enabled(false)
{
  switch (diskFormat) {
    // 88-Disk 8'' inches has 77 tracks and 32 sectors
    case Disk_338K:
      m_trackSize   = diskSectorsPerTrack;
      m_tracksCount = diskTracksCount;
      m_sectorChangeDuration = sectorChangeDurationDisk;  // us
      break;
    // minidisk has 35 tracks and 16 sectors
    case MiniDisk_76K:
      m_trackSize   = minidiskSectorsPerTrack;
      m_tracksCount = minidiskTracksCount;
      m_sectorChangeDuration = sectorChangeDurationMiniDisk;  // us
      break;
  };

  machine->attachDevice(this);

  for (int i = 0; i < DISKCOUNT; ++i) {
    m_readOnlyBuffer[i]   = nullptr;
    m_fileSectorBuffer[i] = nullptr;
    m_file[i]             = nullptr;
    m_track[i]            = 0;
    m_sector[i]           = 0;
    m_pos[i]              = 0;
    m_readByteTime[i]     = 0;
    m_readByteReady[i]    = 1;
    m_sectorChangeTime[i] = 0;
    m_sectorTrue[i]       = 1;
    m_headLoaded[i]       = 1;
  }
}


Mits88Disk::~Mits88Disk()
{
  detachAll();
}


void Mits88Disk::detachAll()
{
  for (int i = 0; i < DISKCOUNT; ++i)
    detach(i);
}


void Mits88Disk::detach(int drive)
{
  flush();
  if (m_readOnlyBuffer[drive]) {
    m_readOnlyBuffer[drive] = nullptr;
  } else if (m_file[drive]) {
    fclose(m_file[drive]);
    m_file[drive] = nullptr;
    delete [] m_fileSectorBuffer[drive];
    m_fileSectorBuffer[drive] = nullptr;
  }
}


void Mits88Disk::attachReadOnlyBuffer(int drive, uint8_t const * data)
{
  detach(drive);
  m_readOnlyBuffer[drive] = data;
}


void Mits88Disk::attachFile(int drive, char const * filename)
{
  detach(drive);

  m_fileSectorBuffer[drive] = new uint8_t[SECTOR_SIZE];

  // file exists?
  struct stat st;
  if (stat(filename, &st) != 0) {
    // file doesn't exist, create and fill with 0xE5
    m_file[drive] = fopen(filename, "w+");
    memset(m_fileSectorBuffer[drive], 0xE5, SECTOR_SIZE);
    for (int i = 0; i < (int) m_trackSize * m_tracksCount; ++i)
      diskWrite(i * SECTOR_SIZE, m_fileSectorBuffer[drive], SECTOR_SIZE, m_file[drive]);
  } else {
    // file already exists, just open for read/write
    m_file[drive] = fopen(filename, "r+");
  }

  flush();
}


// create a file (filename) from specified image (data), and mount it as RW
// file is not created if already exists
void Mits88Disk::attachFileFromImage(int drive, char const * filename, uint8_t const * data)
{
  // file exists?
  struct stat st;
  if (stat(filename, &st) != 0) {
    // file doesn't exist, create and fill with "data" content
    auto imageSize = diskSize();
    auto bufferSize = SECTOR_SIZE * sectorsPerTrack();
    auto buffer = (uint8_t *)malloc(bufferSize);
    auto fw = fopen(filename, "wb");
    while (imageSize > 0) {
      fwrite(data, bufferSize, 1, fw);
      imageSize -= bufferSize;
      data += bufferSize;
    }
    fclose(fw);
    free(buffer);
  }
  attachFile(drive, filename);
}


void Mits88Disk::flush()
{
  for (int i = 0; i < DISKCOUNT; ++i)
    if (m_file[i])
      diskFlush(m_file[i]);
}


int Mits88Disk::readByteFromDisk()
{
  int value = 0;

  if (m_enabled && m_drive > -1 && m_headLoaded[m_drive] == 0) {

    const int track  = m_track[m_drive];
    const int sector = m_sector[m_drive];
    const int pos    = m_pos[m_drive];

    if (m_readOnlyBuffer[m_drive]) {
      int position = (int) m_trackSize * SECTOR_SIZE * track + sector * SECTOR_SIZE + pos;
      value = m_readOnlyBuffer[m_drive][position];
    } else if (m_file[m_drive]) {
      if (pos == 0) {
        // prefetch entire track if required
        fetchFileData(m_file[m_drive], (int) m_trackSize * SECTOR_SIZE * track, (int) m_trackSize * SECTOR_SIZE);
        // read the entire sector into the buffer
        int position = (int) m_trackSize * SECTOR_SIZE * track + sector * SECTOR_SIZE;
        diskRead(position, m_fileSectorBuffer[m_drive], SECTOR_SIZE, m_file[m_drive]);
      }
      value = m_fileSectorBuffer[m_drive][pos];
    } else
      value = 0xFF;

    //fprintf(stderr, "%lld: read d=%d t=%d s=%d p=%d =>%02x\n", m_tick, m_drive, m_track[m_drive], m_sector[m_drive], m_pos[m_drive], value);

    m_pos[m_drive] = (pos + 1) % SECTOR_SIZE;

  }

  return value;
}


void Mits88Disk::writeByteToDisk(int value)
{
  if (m_enabled && m_drive > -1 && m_headLoaded[m_drive] == 0) {

    if (m_file[m_drive] && m_pos[m_drive] < SECTOR_SIZE) {
      if (m_pos[m_drive] == 0) {
        // prefetch entire track if required
        fetchFileData(m_file[m_drive], (int) m_trackSize * SECTOR_SIZE * m_track[m_drive], (int) m_trackSize * SECTOR_SIZE);
      }

      int position = (int) m_trackSize * SECTOR_SIZE * m_track[m_drive] + m_sector[m_drive] * SECTOR_SIZE + m_pos[m_drive];
      uint8_t b = value;
      diskWrite(position, &b, 1, m_file[m_drive]);

      //fprintf(stderr, "%lld: write d=%d t=%d s=%d p=%d v=%02x\n", m_tick, m_drive, m_track[m_drive], m_sector[m_drive], m_pos[m_drive], value);

      m_pos[m_drive] += 1;
    }

  }
}


bool Mits88Disk::read(int address, int * result)
{
  //fprintf(stderr, "%lld: read(%02x)\n", m_tick, address);
  switch (address) {
    case 0x08:
      // Drive Status
      if (m_enabled && m_drive > -1) {
        int track0 = (m_track[m_drive] == 0 ? 0 : 1);
        *result = 0b00100000 | (track0 << 6) | (m_readByteReady[m_drive] << 7) | (m_headLoaded[m_drive] << 2);
        //fprintf(stderr, "%lld: status: track0=%s byteReady=%s\n", m_tick, track0?"F":"T", m_readByteReady[m_drive]?"F":"T");
      } else {
        *result = 0b11100111;
        //fprintf(stderr, "%lld: status: DISABLED\n", m_tick);
      }
      return true;

    case 0x09:
      // Sector Number
      if (m_enabled && m_drive > -1 && m_headLoaded[m_drive] == 0) {
        *result = (m_sector[m_drive] << 1) | m_sectorTrue[m_drive];
        //fprintf(stderr, "%lld: ask sector: num=%d sectorTrue=%s\n", m_tick, m_sector[m_drive], m_sectorTrue[m_drive]?"F":"T");
      } else {
        *result = 0xff;
        //fprintf(stderr, "%lld: ask sector: num=DISABLED\n", m_tick);
      }
      return true;

    case 0x0A:
      // read data
      if (m_enabled && m_drive > -1 && m_headLoaded[m_drive] == 0) {
        *result = readByteFromDisk();
        m_readByteReady[m_drive] = 1; // byte not ready
        m_readByteTime[m_drive] = m_tick;
      } else {
        *result = 0;
      }
      return true;

    default:
      return false;
  }
}


bool Mits88Disk::write(int address, int value)
{
  //fprintf(stderr, "%lld: write(%02x, %02x)\n", m_tick, address, value);
  switch (address) {

    case 0x08:
      //  Drive Select
      if (value & 0x80) {
        m_enabled = false;
        if (value != 0xff)
          setDrive(value & 0xF);
      } else {
        m_enabled = true;
        setDrive(value & 0xF);

        m_readByteReady[m_drive] = 1; // byte not ready
        m_readByteTime[m_drive] = 0;
        m_sectorChangeTime[m_drive] = m_tick;
        m_sector[m_drive] = 0;
        m_pos[m_drive] = 0;
        m_sectorTrue[m_drive] = 1;

        // on minidisk head is loaded when a drive is selected
        if (m_diskFormat == MiniDisk_76K)
          m_headLoaded[m_drive] = 0;
      }

      //fprintf(stderr, "%lld: drive select=%d\n", m_tick, m_drive);
      return true;

    case 0x09:
      // Drive control
      if (m_drive > -1) {
        if ((value & (1 | 2))) {
          // change track
          if (value & 1)
            m_track[m_drive] = (m_track[m_drive] < m_tracksCount - 1 ? m_track[m_drive] + 1 : m_tracksCount - 1);
          else if (value & 2)
            m_track[m_drive] = (m_track[m_drive] > 0 ? m_track[m_drive] - 1 : 0);

          m_readByteReady[m_drive] = 1; // byte not ready
          m_readByteTime[m_drive] = 0;
          m_sectorChangeTime[m_drive] = m_tick;
          m_sector[m_drive] = 0;
          m_pos[m_drive] = 0;
          m_sectorTrue[m_drive] = 1;

          //fprintf(stderr, "%lld: selected track=%d\n", m_tick, m_track[m_drive]);
        }
        if (value & 4) {
          // head load
          m_enabled = true;
          m_headLoaded[m_drive] = 0;
        }
        if (value & 8) {
          // head unload
          m_headLoaded[m_drive] = 1;
        }
      }
      return true;

    case 0x0A:
      // write data
      if (m_enabled && m_drive > -1 && m_headLoaded[m_drive] == 0)
        writeByteToDisk(value);
      return true;

    default:
      return false;
  }
}


void Mits88Disk::tick(int ticks)
{
  m_tick += ticks;

  if (m_enabled == false || m_drive == -1 || m_headLoaded[m_drive] == 1)
    return;

  if (m_tick >= m_sectorChangeTime[m_drive] + m_sectorChangeDuration
      || (m_tick >= m_sectorChangeTime[m_drive] + sectorTrueDuration + readByteDuration + sectorChangeShortDuration && m_pos[m_drive] == 0)) {
    // it is time to change sector
    m_sector[m_drive] = (m_sector[m_drive] + 1) % m_trackSize;
    //fprintf(stderr, "%lld: new sector=%d track=%d\n", m_tick, m_sector[m_drive], m_track[m_drive]);

    m_readByteReady[m_drive] = 0;
    m_sectorTrue[m_drive] = 0;
    m_readByteTime[m_drive] = m_tick;
    m_sectorChangeTime[m_drive] = m_tick;
    m_pos[m_drive] = 0;
  }

  if (m_readByteTime[m_drive] > 0 && m_tick >= m_readByteTime[m_drive] + readByteDuration) {
    m_readByteReady[m_drive] = 0; // byte ready
  }

  if (m_tick >= m_sectorChangeTime[m_drive] + sectorTrueDuration) {
    m_sectorTrue[m_drive] = 1;
  }

}



void Mits88Disk::setDrive(int value)
{
  m_drive = fabgl::iclamp(value, 0, DISKCOUNT - 1);
}



void Mits88Disk::sendDiskImageToStream(int drive, Stream * stream)
{
  const int prevDrive = m_drive;
  const int prevTrack = m_track[m_drive];

  setDrive(drive);

  for (int t = 0; t < m_tracksCount; ++t) {
    m_track[m_drive] = t;
    for (int s = 0; s < m_trackSize; ++s) {
      m_sector[m_drive] = s;
      m_pos[m_drive] = 0;
      for (int b = 0; b < SECTOR_SIZE; ++b) {
        int v = readByteFromDisk();
        stream->write(v);
      }
    }
  }

  setDrive(prevDrive);
  m_track[m_drive] = prevTrack;
}



void Mits88Disk::receiveDiskImageFromStream(int drive, Stream * stream)
{
  const int prevDrive = m_drive;
  const int prevTrack = m_track[m_drive];

  setDrive(drive);

  for (int t = 0; t < m_tracksCount; ++t) {
    m_track[m_drive] = t;
    for (int s = 0; s < m_trackSize; ++s) {
      m_sector[m_drive] = s;
      m_pos[m_drive] = 0;
      for (int b = 0; b < SECTOR_SIZE; ++b) {
        while (stream->available() == 0)
          ;
        int v = stream->read();
        writeByteToDisk(v);
      }
      writeByteToDisk(0);   // flush
      stream->write(0x06);  // ACK
    }
  }

  setDrive(prevDrive);
  m_track[m_drive] = prevTrack;
}




// Mits88Disk disk drive controller
////////////////////////////////////////////////////////////////////////////////////
